mlab-modules/MPPB01/doc/parallella_schematic.pdf

# Page List

Page | Content

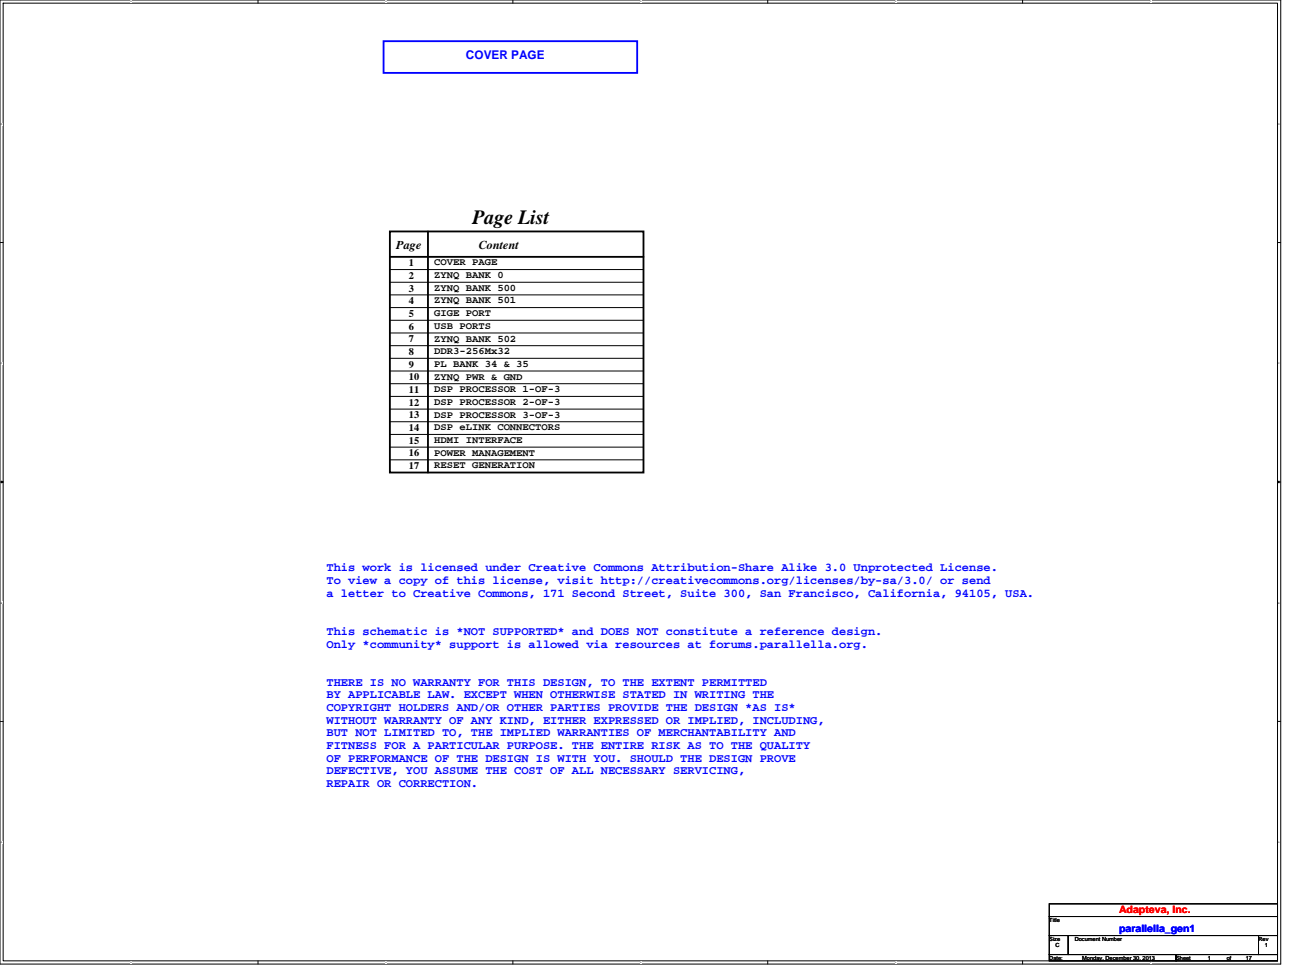
[picture p14: page 1]
COVER PAGE; Title; parallella_gen1; Adapteva, Inc.

1 | COVER PAGE
2 | ZYNQ BANK 0
3 | ZYNQ BANK 500
4 | ZYNQ BANK 501
5 | GIGE PORT
6 | USB PORTS
7 | ZYNQ BANK 502
8 | DDR3-256Mx32
9 | PL BANK 34 & 35
10 | ZYNQ PWR & GND
11 | DSP PROCESSOR 1-OF-3
12 | DSP PROCESSOR 2-OF-3
13 | DSP PROCESSOR 3-OF-3
14 DSP eLINK CONNECTORS
15 | HDMI INTERFACE
16 POWER MANAGEMENT
17 RESET GENERATION

This work is licensed under Creative Commons Attribution-Share Alike 3.0 Unprotected License.
To view a copy of this license, visit http://creativecommons.org/licenses/by-sa/3.0/ or send
a letter to Creative Commons, 171 Second Street, Suite 300, San Francisco, California, 94105, USA.

This schematic is *NOT SUPPORTED* and DOES NOT constitute a reference design.
Only *community* support is allowed via resources at forums.parallella.org.

THERE IS NO WARRANTY FOR THIS DESIGN, TO THE EXTENT PERMITTED
BY APPLICABLE LAW. EXCEPT WHEN OTHERWISE STATED IN WRITING THE
COPYRIGHT HOLDERS AND/OR OTHER PARTIES PROVIDE THE DESIGN *AS IS*
WITHOUT WARRANTY OF ANY KIND, EITHER EXPRESSED OR IMPLIED, INCLUDING,
BUT NOT LIMITED TO, THE IMPLIED WARRANTIES OF MERCHANTABILITY AND
FITNESS FOR A PARTICULAR PURPOSE. THE ENTIRE RISK AS TO THE QUALITY
OF PERFORMANCE OF THE DESIGN IS WITH YOU. SHOULD THE DESIGN PROVE
DEFECTIVE, YOU ASSUME THE COST OF ALL NECESSARY SERVICING,
REPAIR OR CORRECTION.

Size C | Document Number | Rev

Date: Monday, December 30, 2013 Monday, December 30, 2013 Monday, December 30, 2013 | Sheet 1 1 1 of 17 17 17

# ZYNQ BANK0

# BANK 0

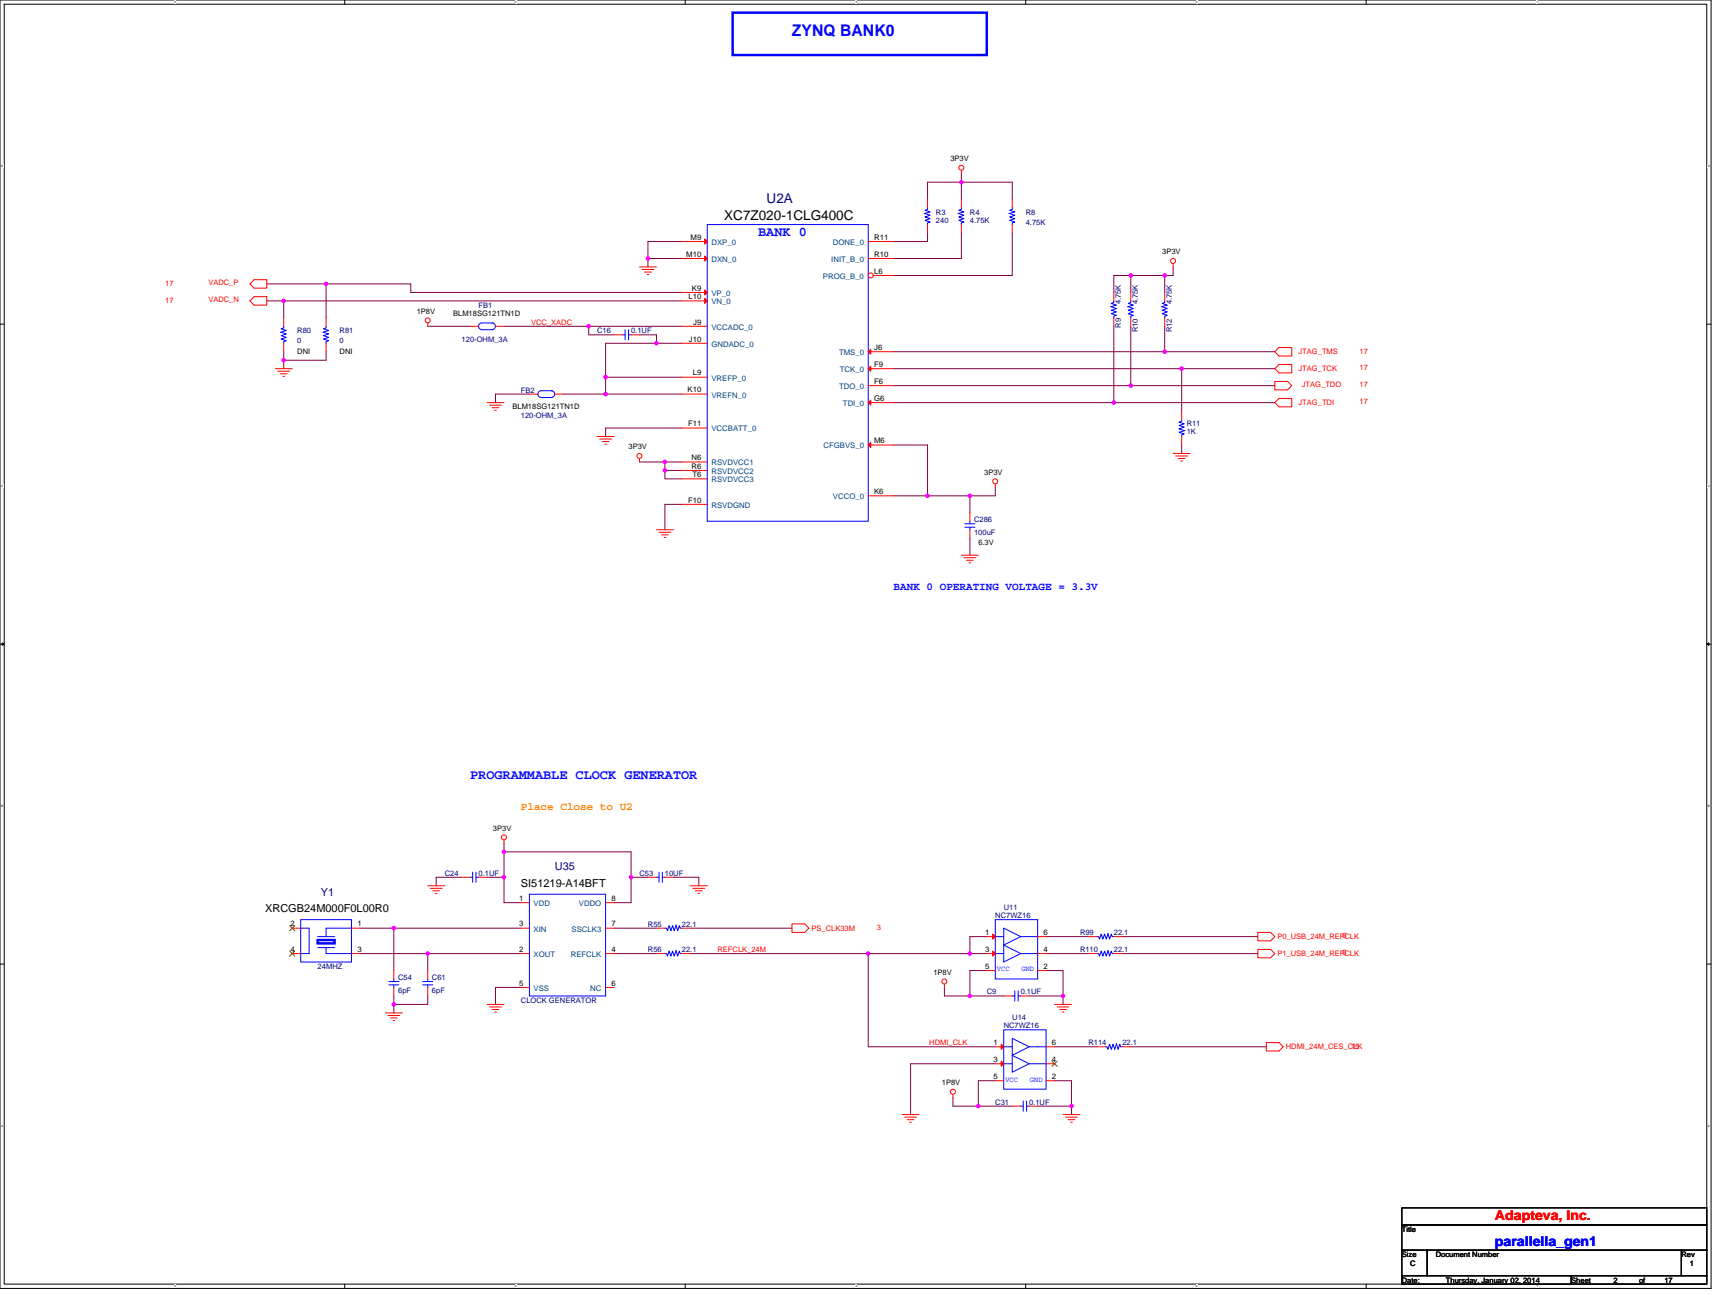
[picture p15: page 2]

# ZYNQ BANK 500

# QUAD SPI FLASH

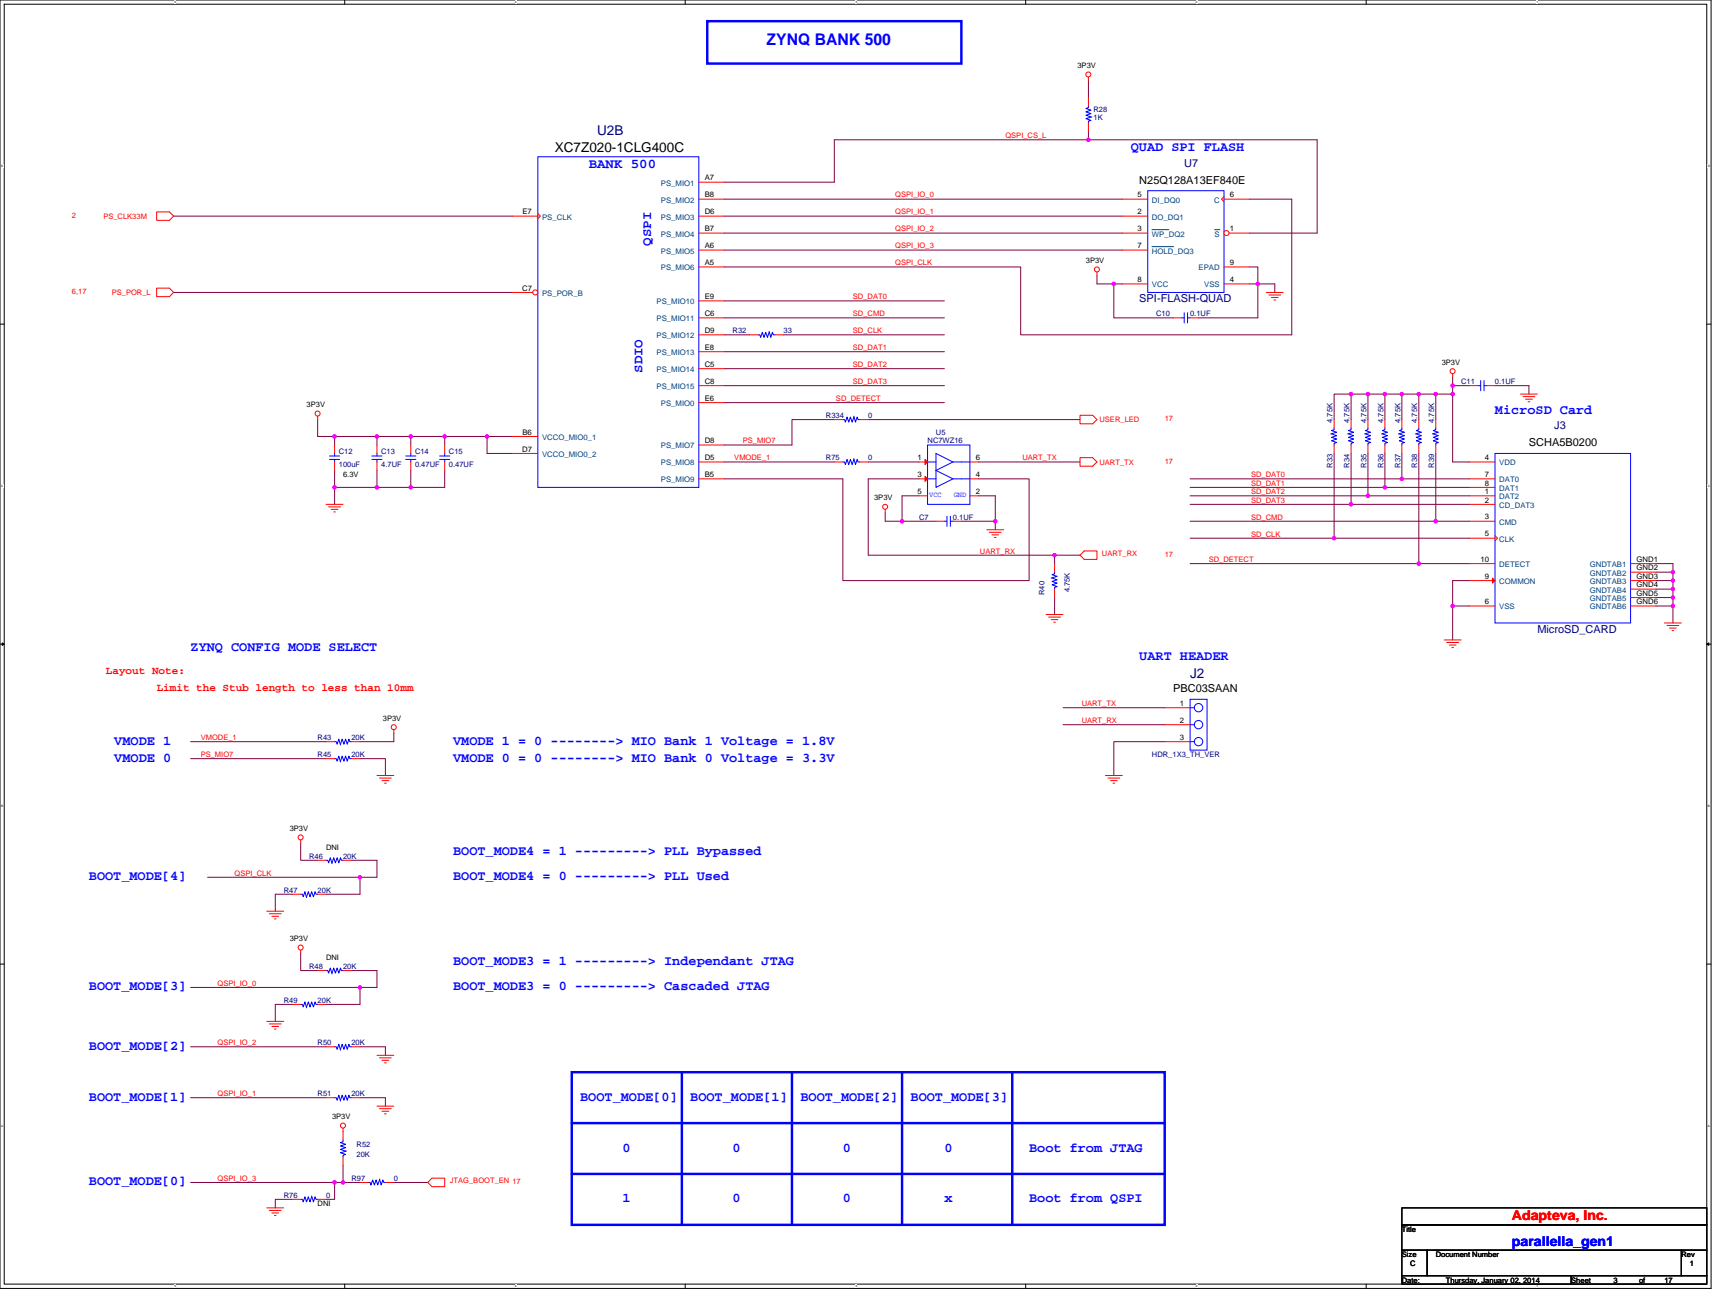
[picture p16: page 3]

ZYNQ CONFIG MODE SELECT

Limit the Stub length to less than 10mm

VMODE 1 = 0 --------> MIO Bank 1 Voltage = 1.8V
VMODE 0 = 0 --------> MIO Bank 0 Voltage = 3.3V

0 | 0 | 0 | 0 | Boot from JTAG

1 | | 0 0 | x | Boot from QSPI

# ZYNQ BANK 501

# BANK 501

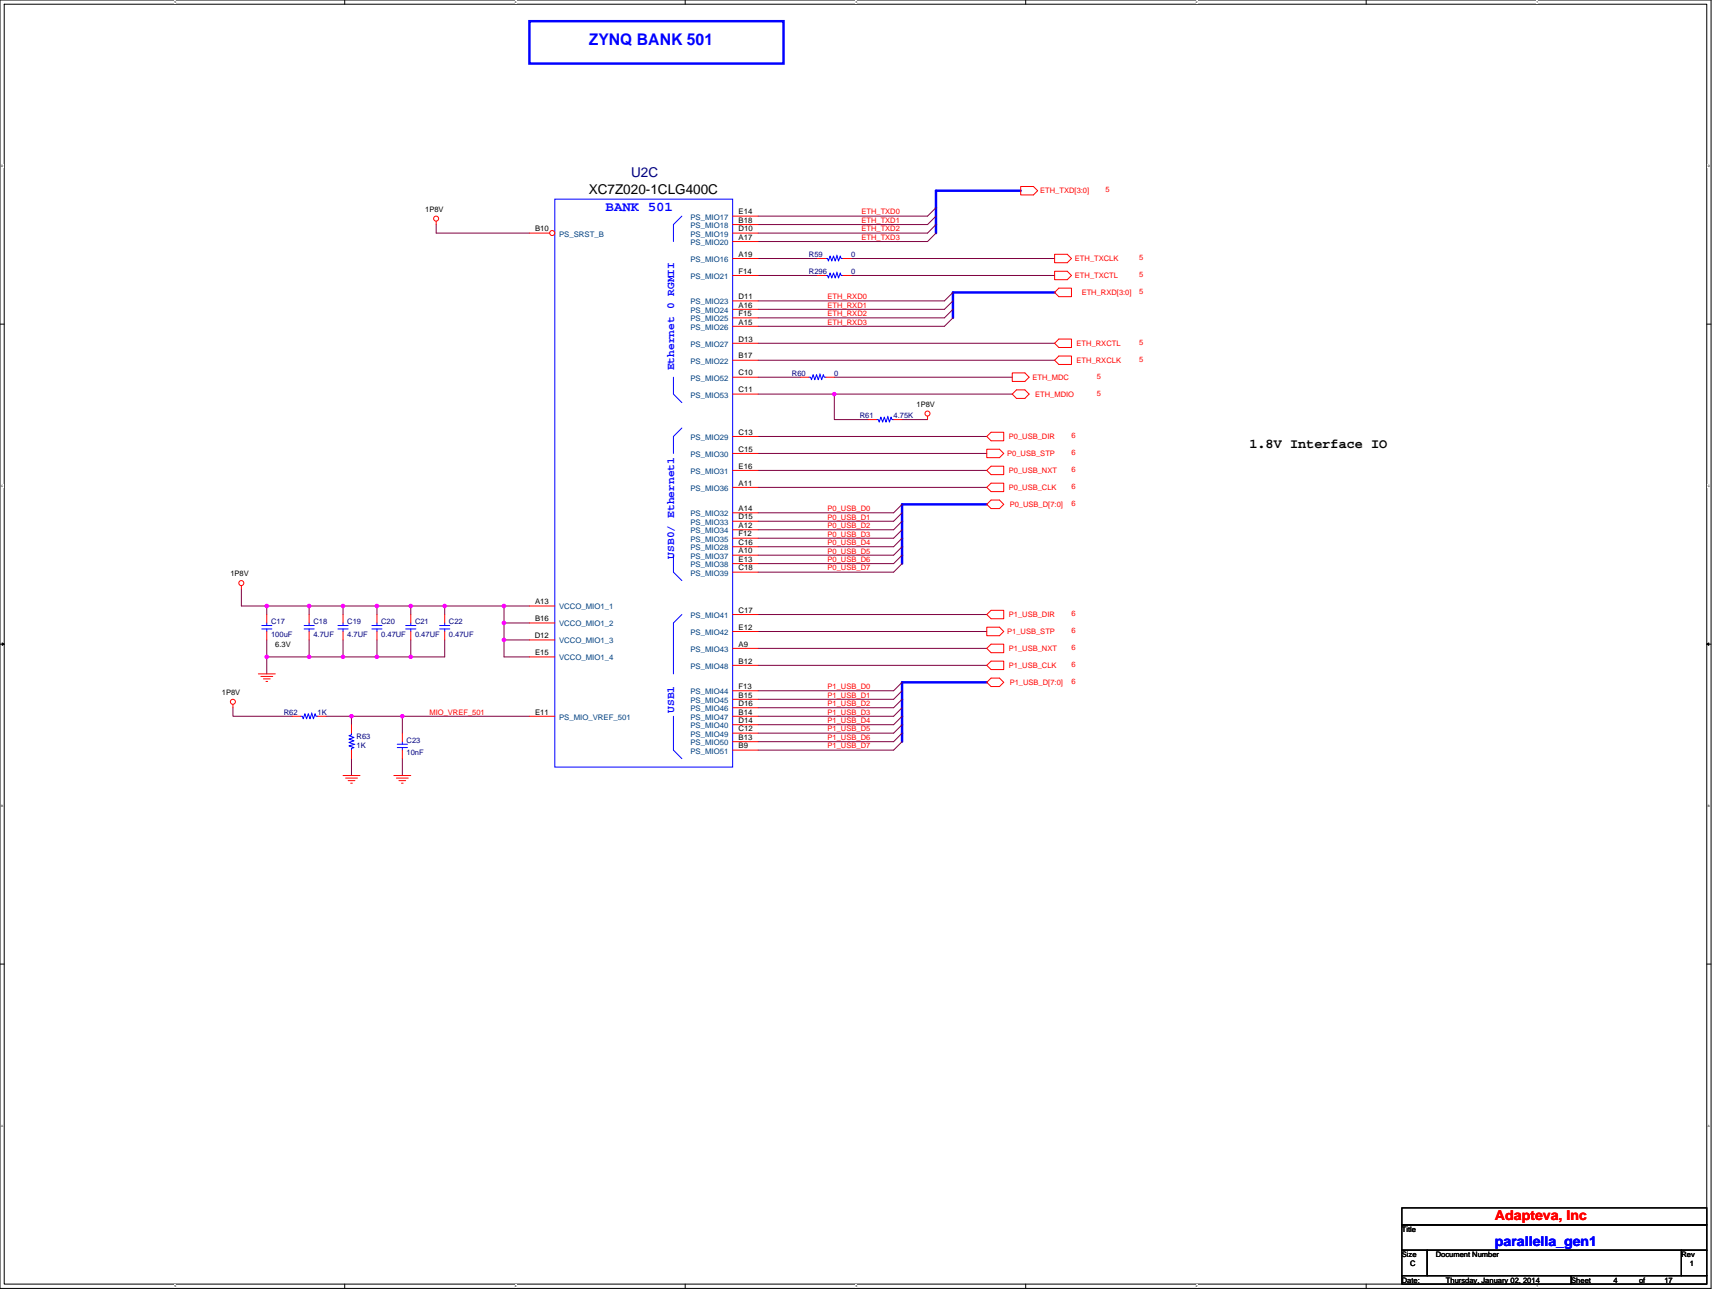
[picture p17: page 4]

## 100 Ohm Differential

# GIGE PHY

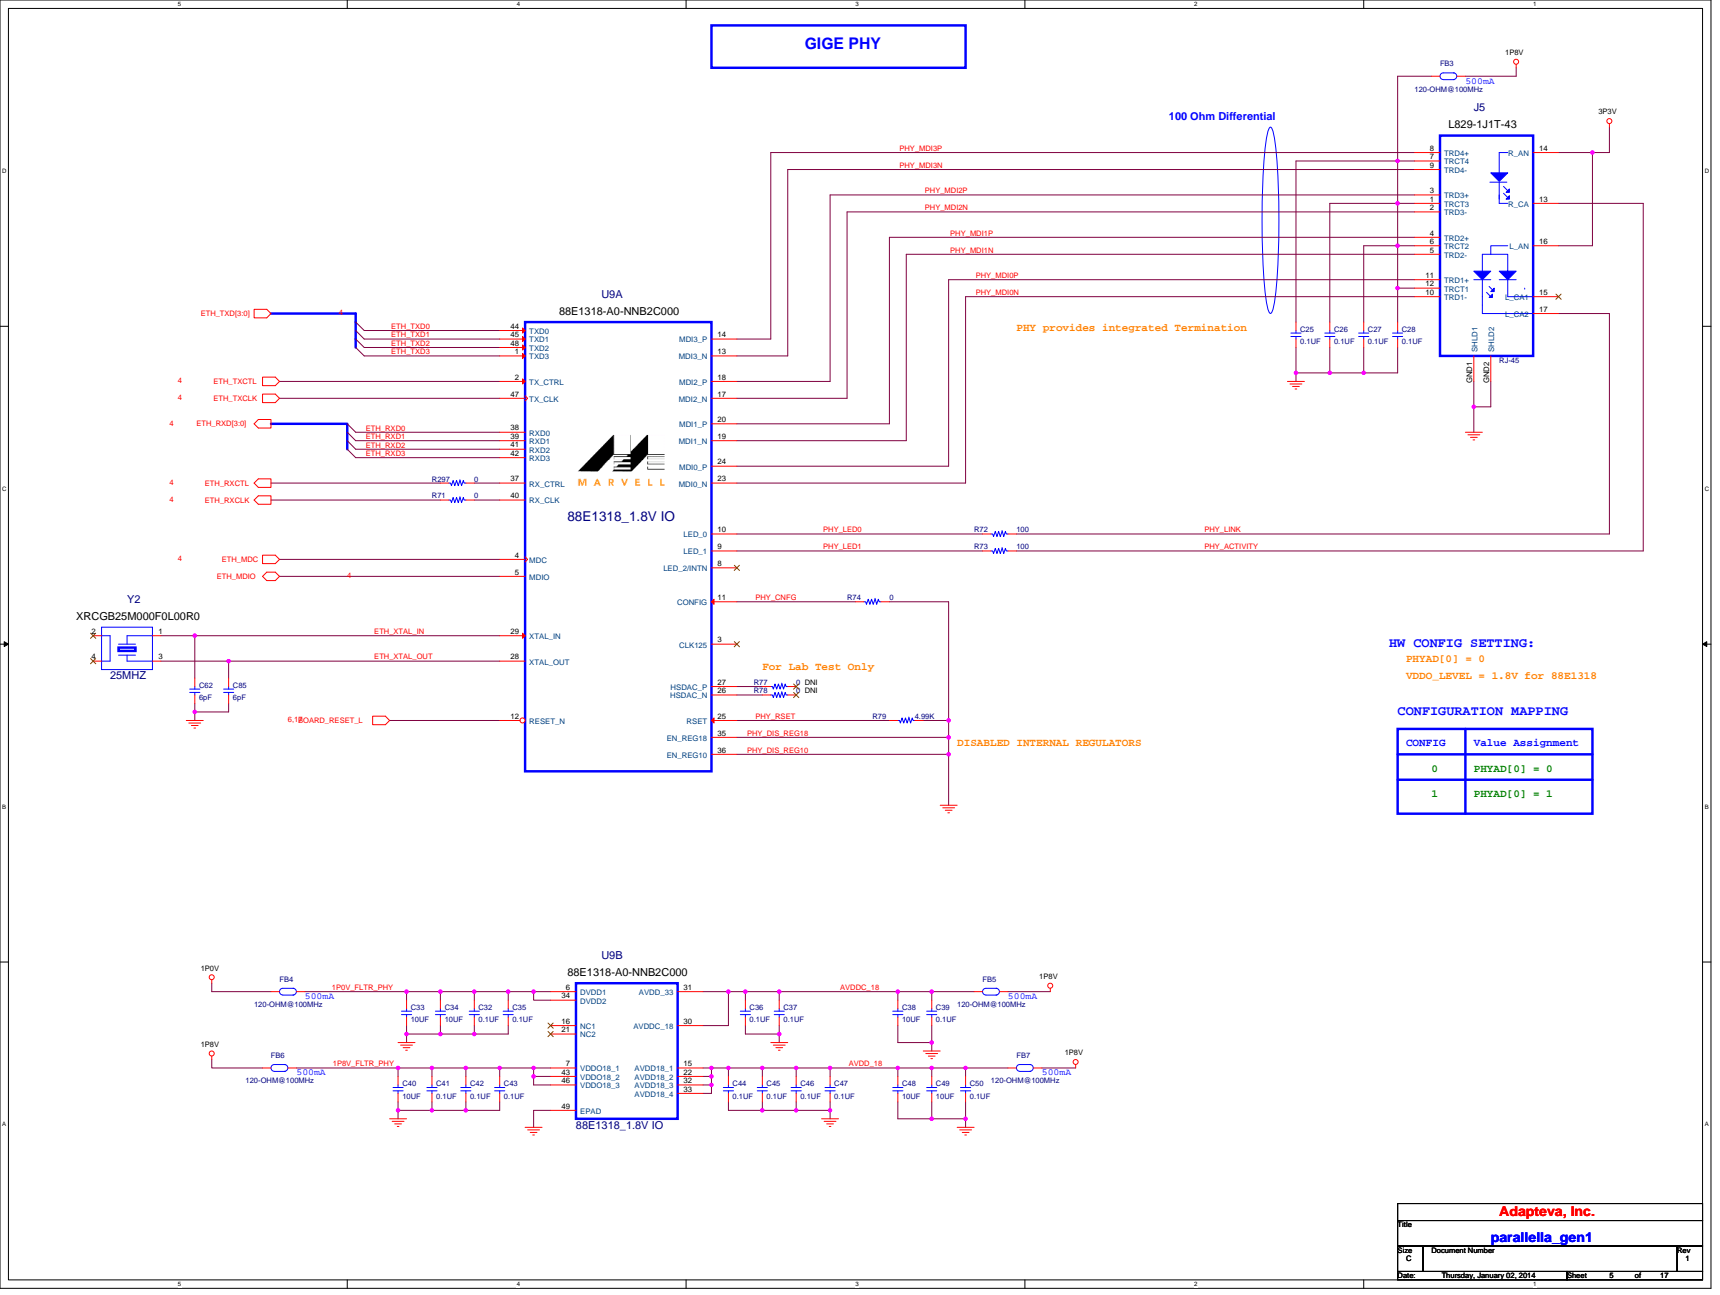
[picture p18: page 5]

TRCT4 7
TRD4- 9

PHY_MDI2P | | TRD3+ 3
PHY_MDI2N | | TRCT3 1

PHY_MDI1P | | TRD2+ 4
PHY_MDI1N | | | TRCT2 6

TRD2- 5

PHY_MDI0P | | TRCT1 12 TRD1+ 11

PHY_MDI0N

PHY provides integrated Termination

3 | ETH_XTAL_OUT | XTAL_OUT 28

For Lab Test Only

RESET_N 12

CONFIG | Value Assignment

0 | PHYAD[0] = 0

1 | PHYAD[0] = 1

# USB PORTS

## 100-ohm Differential

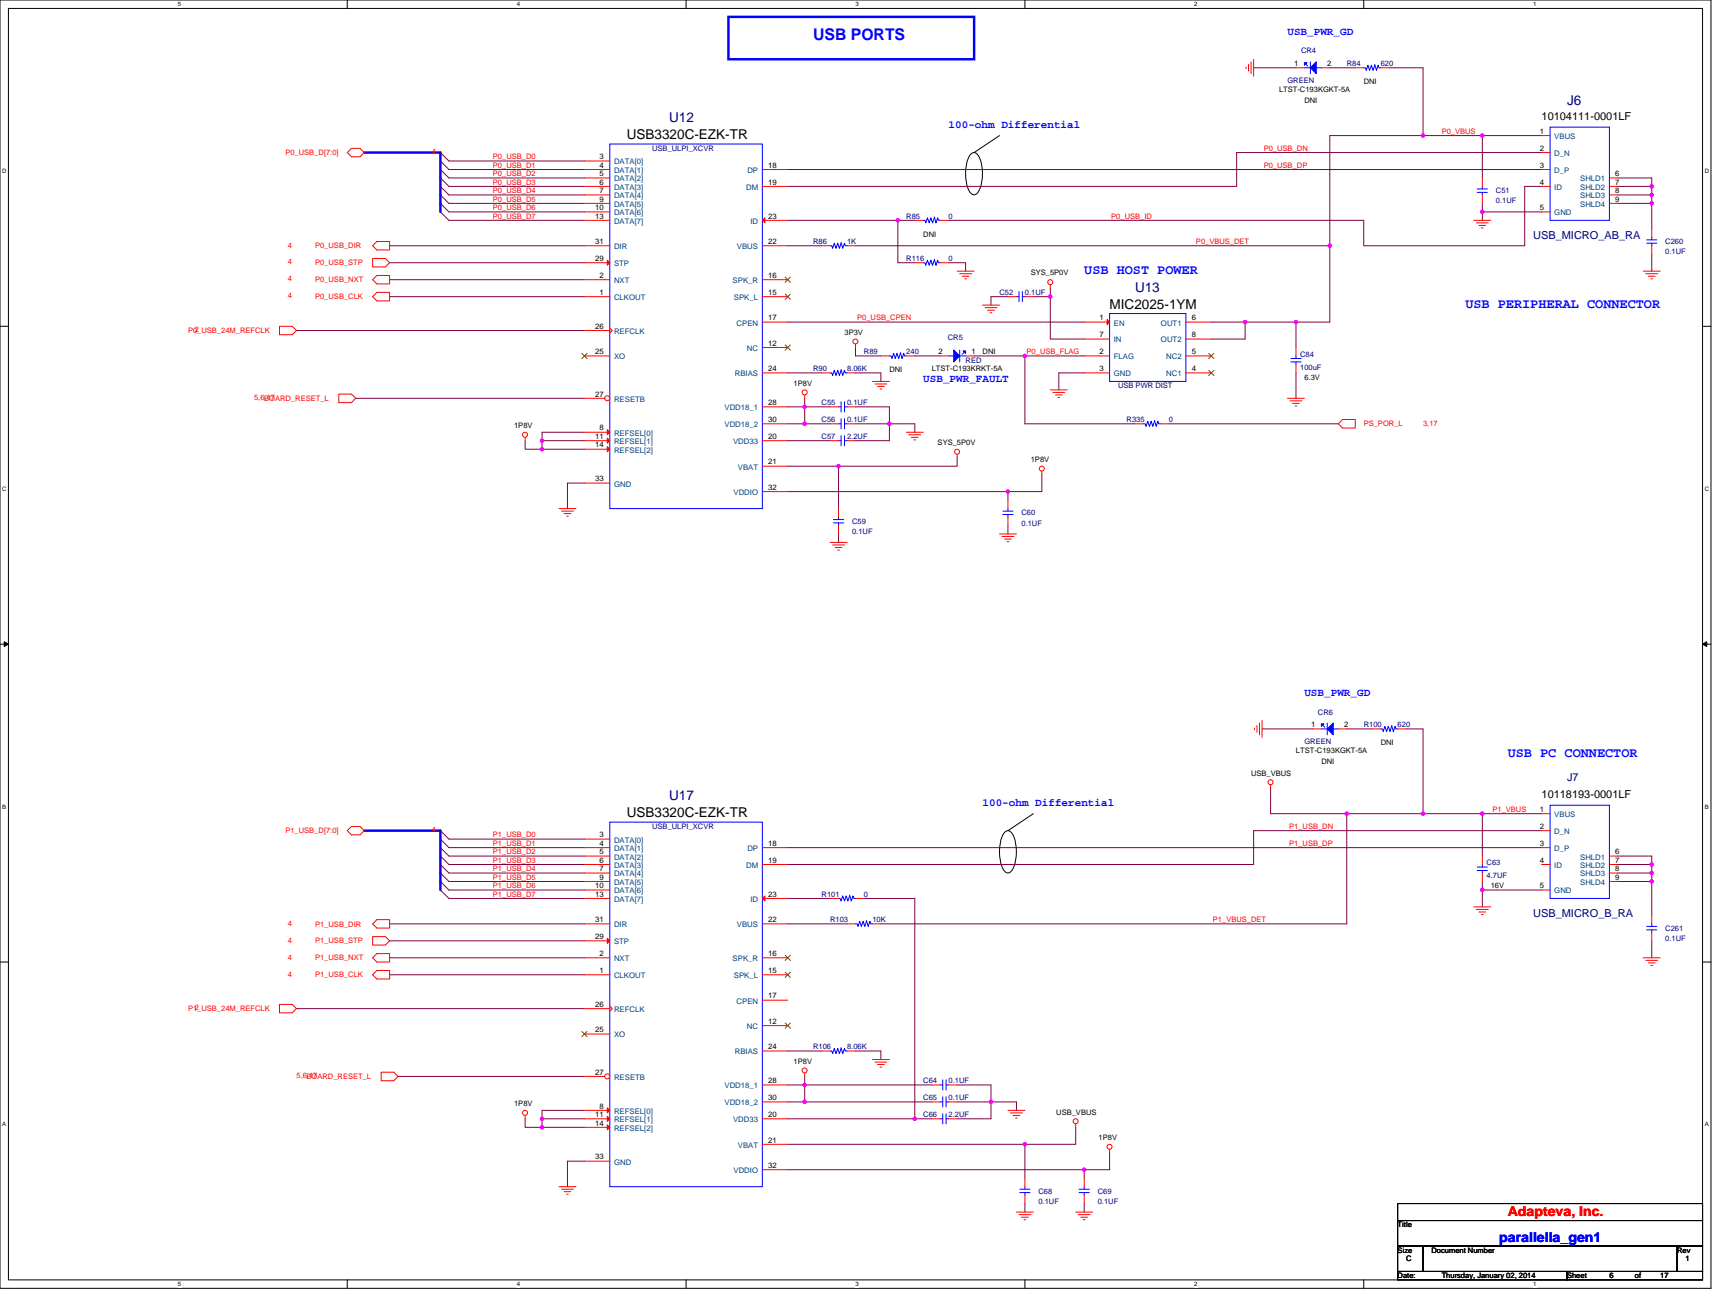
[picture p19: page 6]

P0_USB_DP | D_P 3

P1_USB_DP | | D_P 3

GND 5

# ZYNQ BANK 502

# BANK 502

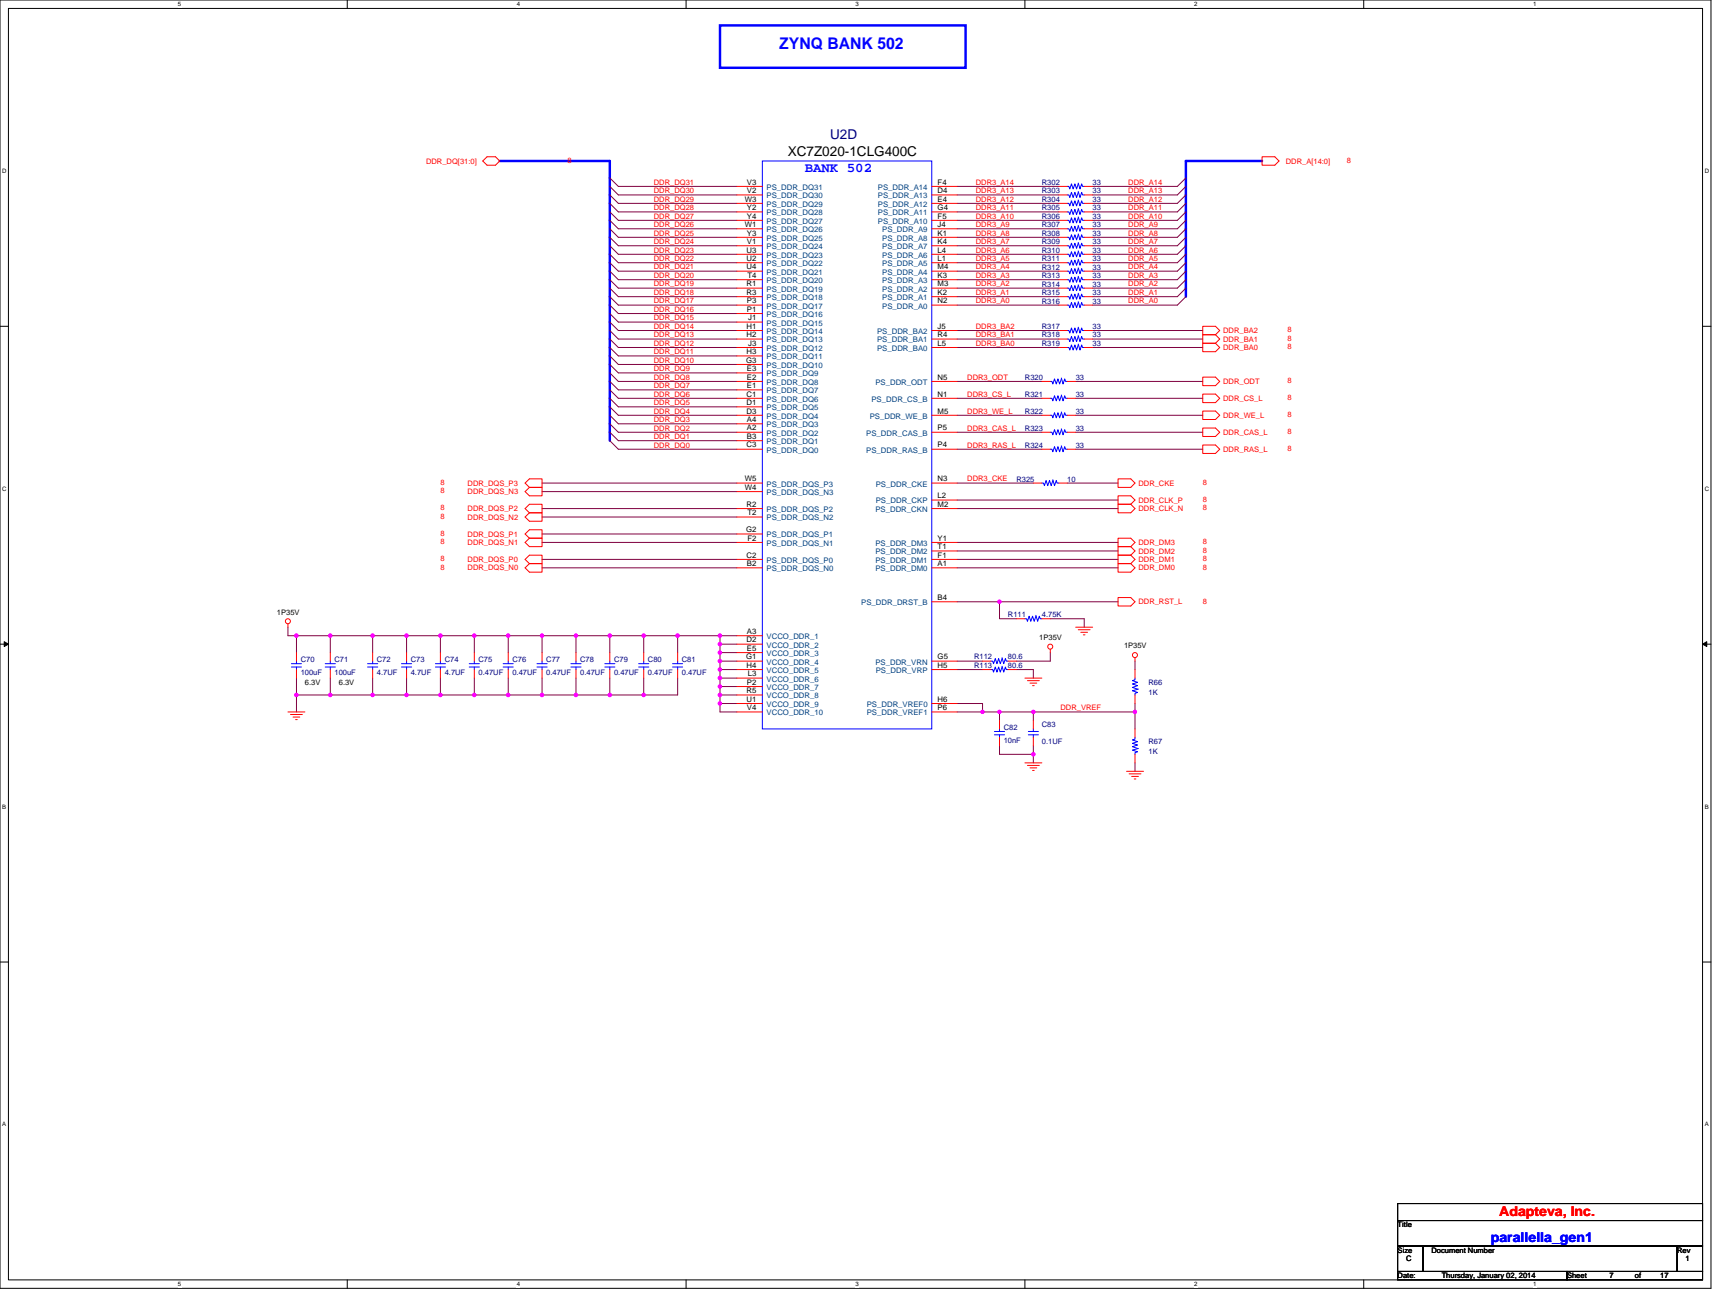
[picture p20: page 7]

# DDR3 - 256M X 32

U20

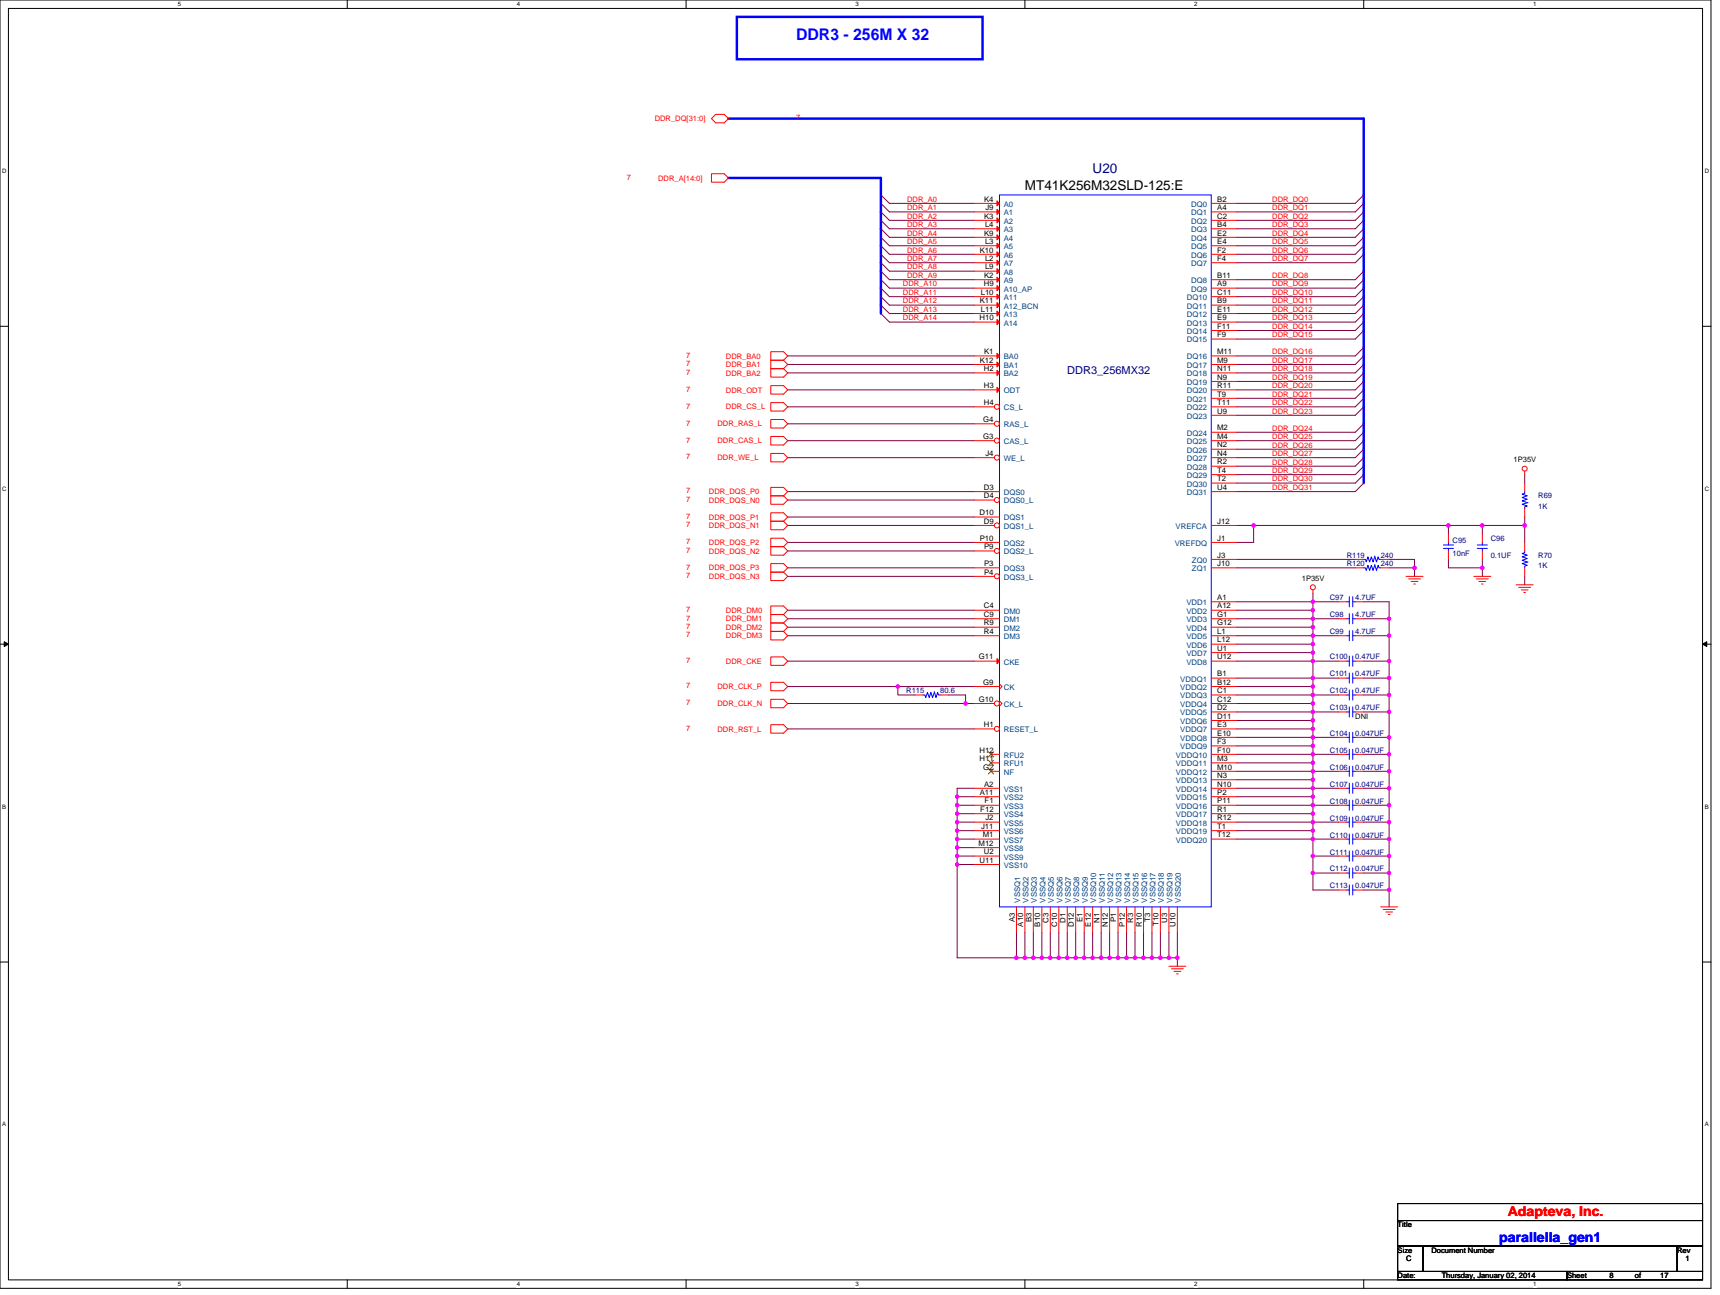
[picture p21: page 8]

# BANKS 34 & 35

# Enable 100-ohm internal termination on all LVDS inputs

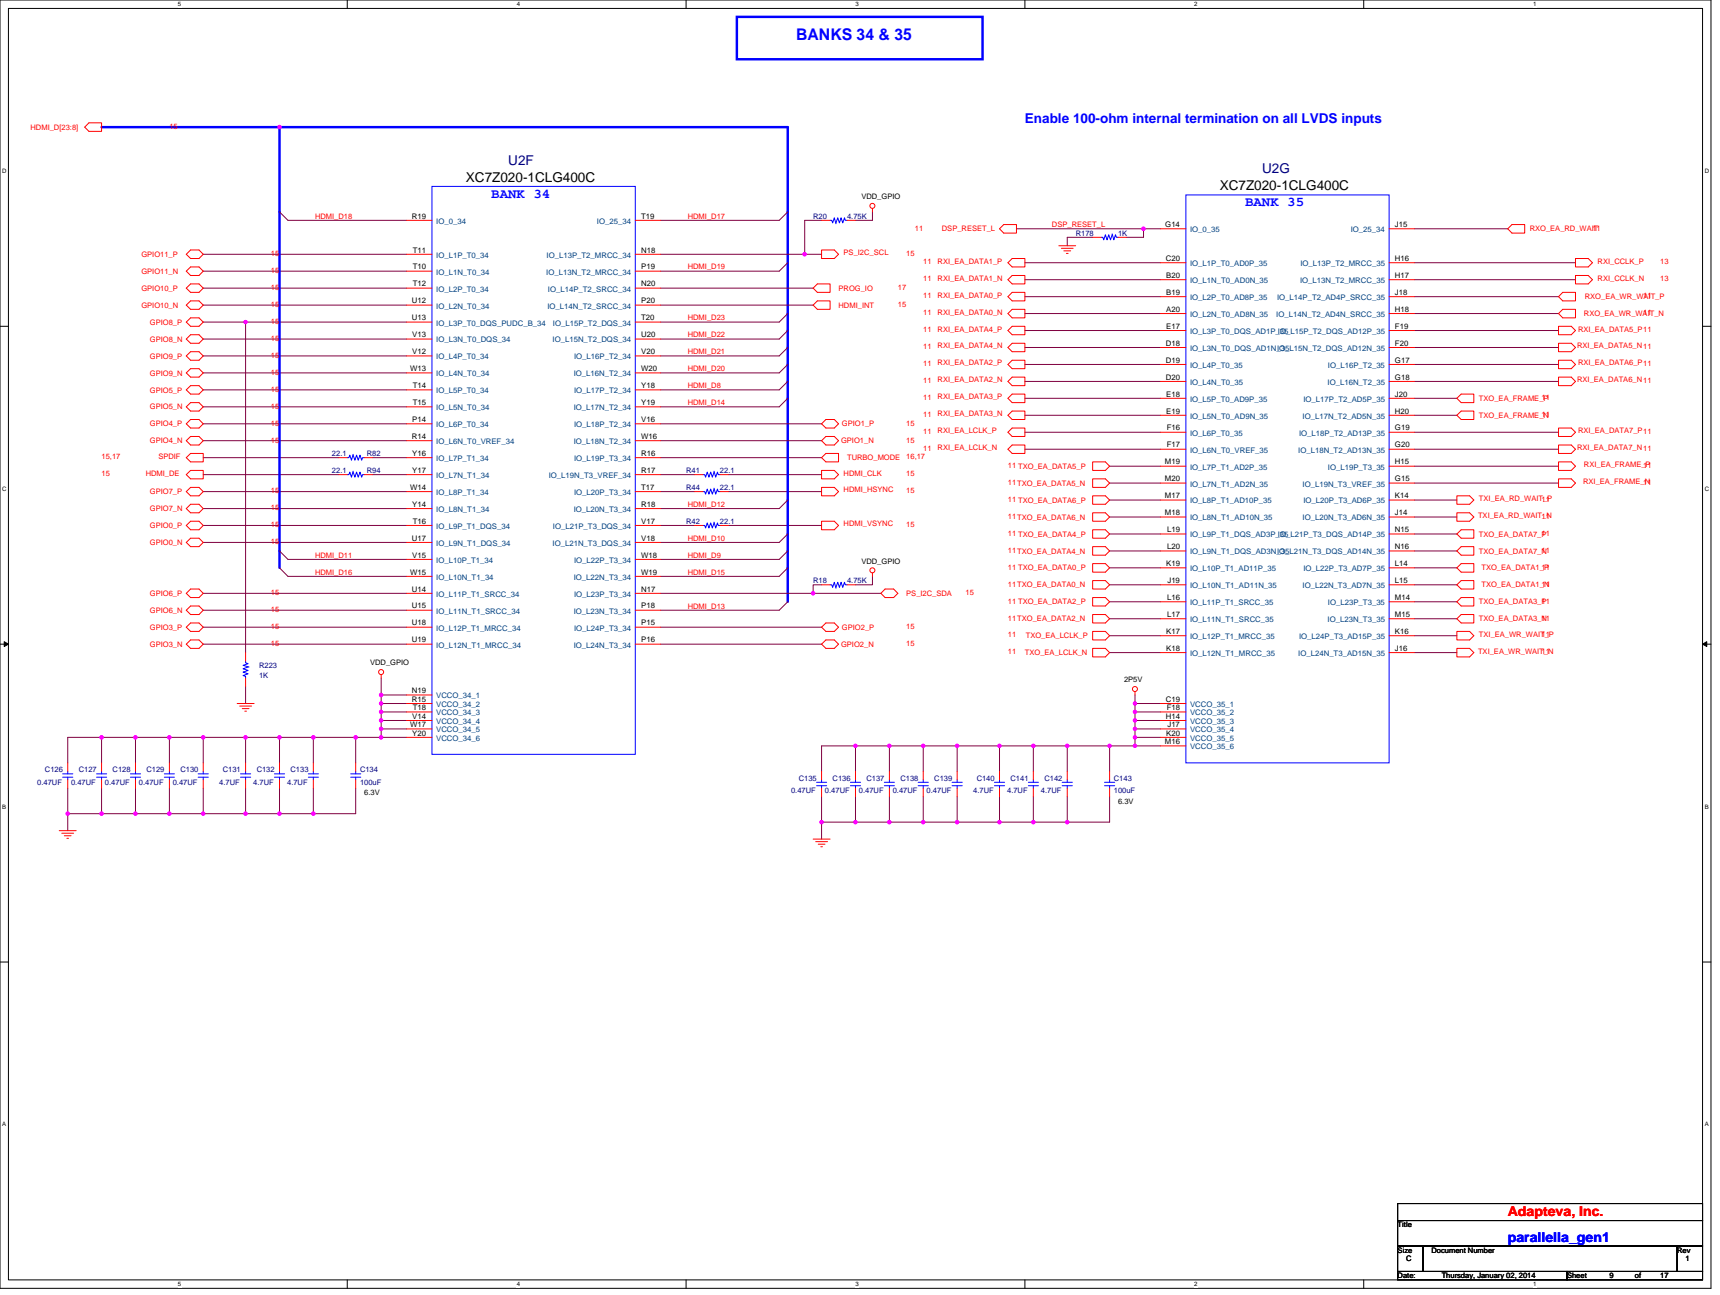
[picture p22: page 9]

IO_L3P_T0_DQS_PUDC_B_34 U13 | HDMI_D23 HDMI_D22 HDMI_D21 HDMI_D20 HDMI_D8 HDMI_D14

IO_L3N_T0_DQS_34 V13

IO_L6N_T0_VREF_34 R14

IO_L9N_T1_DQS_34 U17

# ZYNQ POWER & GROUND

# PWR/GND

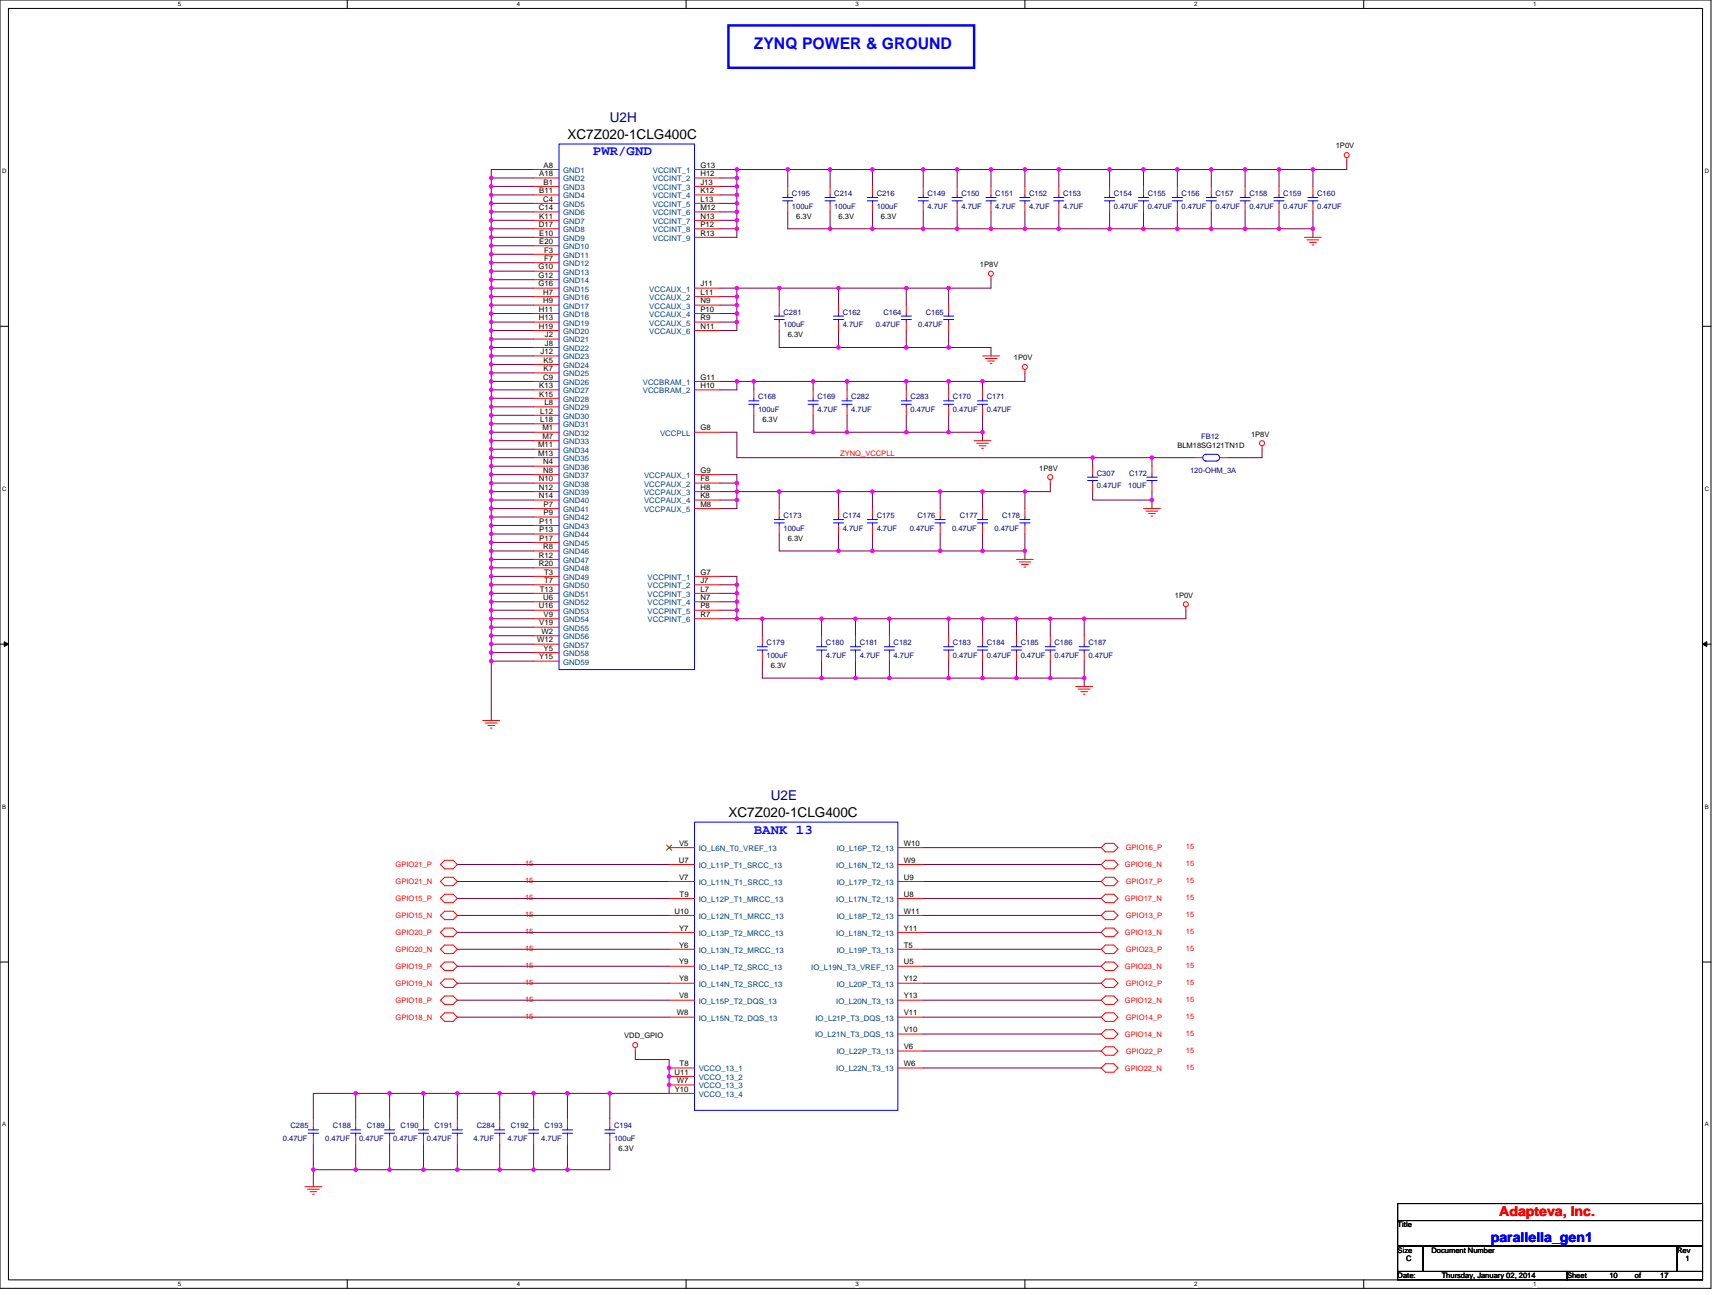
[picture p23: page 10]

# DSP PROCESSOR 1-OF-3

# CONTROL/MONITOR

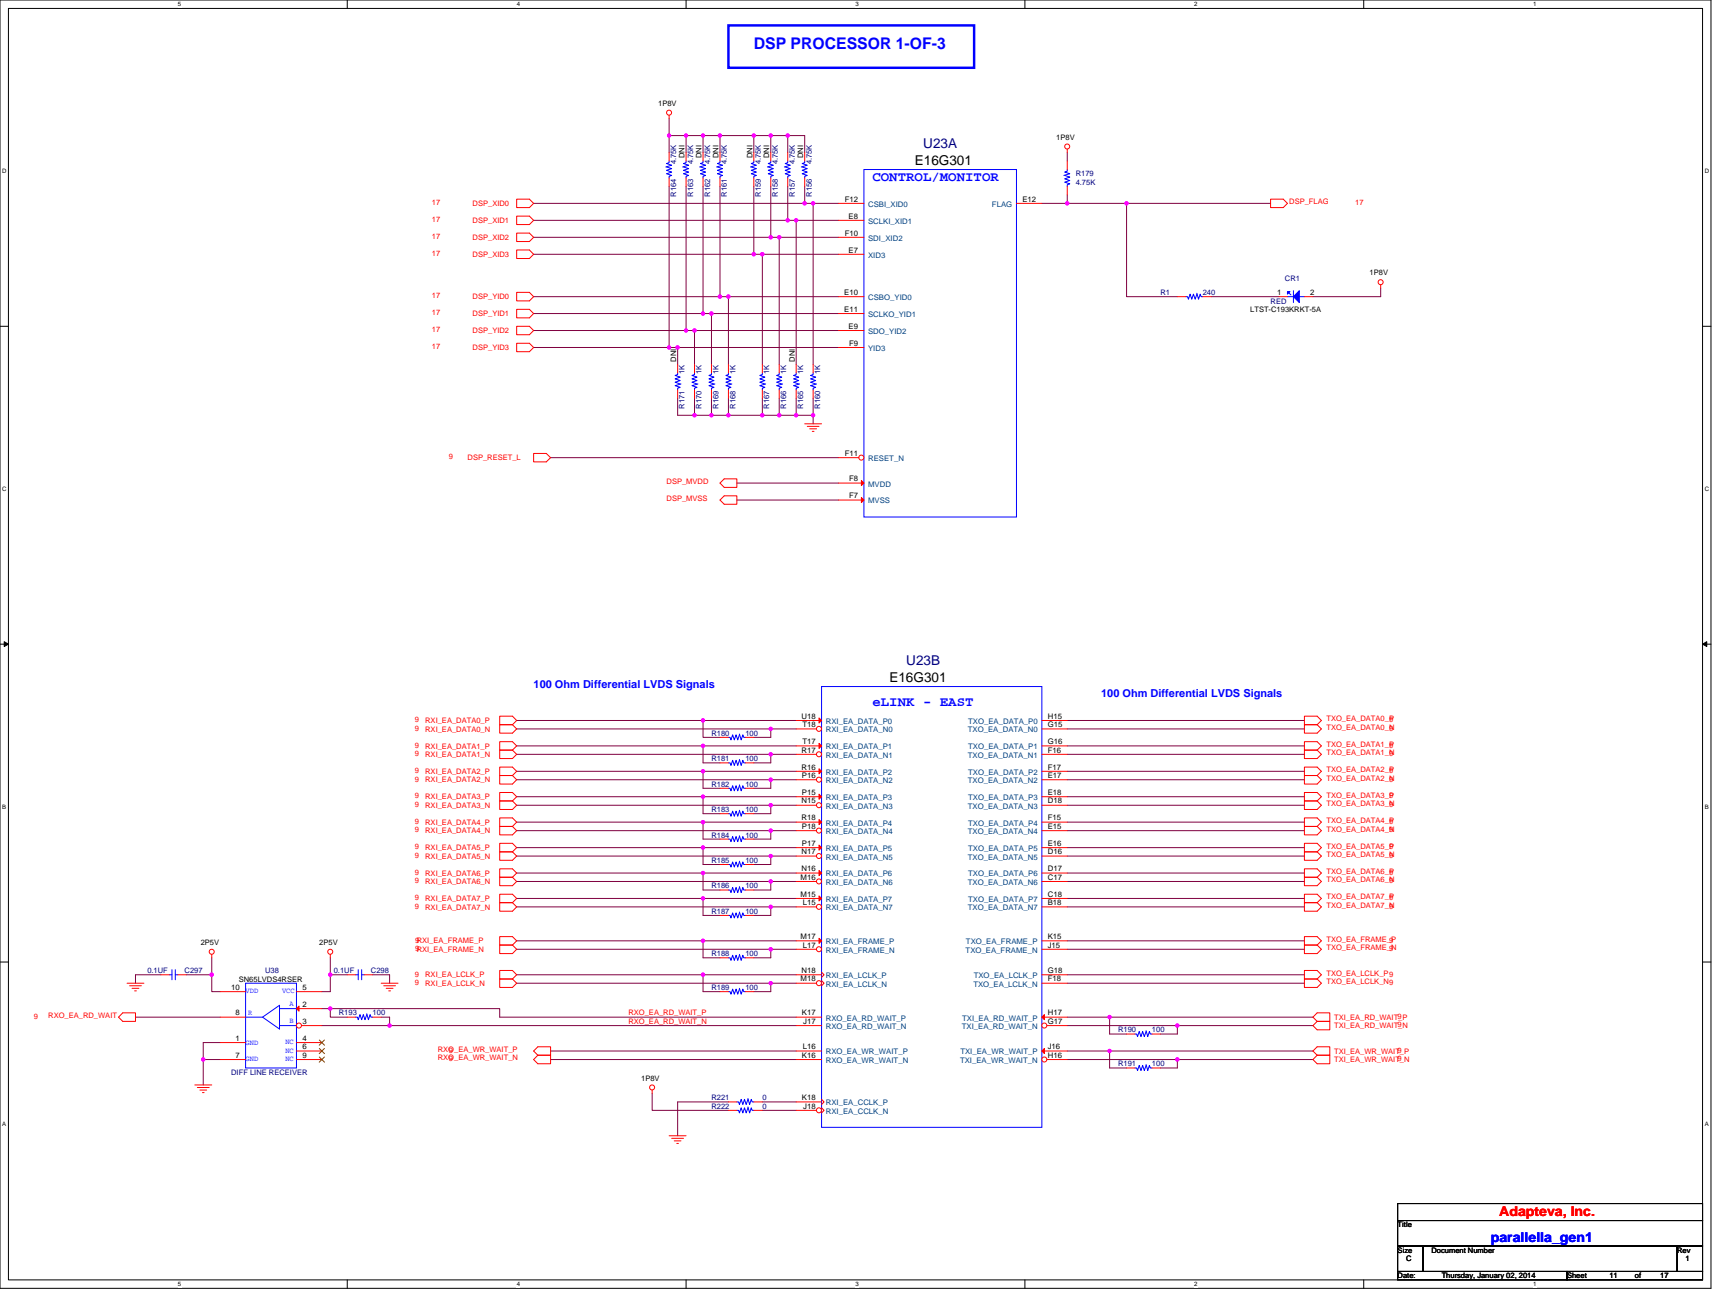
[picture p24: page 11]

SCLKI_XID1 E8

SDI_XID2 F10

XID3 E7

CSBO_YID0 E10

SCLKO_YID1 E11

SDO_YID2 E9

YID3 F9

100 Ohm Differential LVDS Signals

RXI_EA_DATA_N1 R17 RXI_EA_DATA_P2 R16

RXI_EA_DATA_N2 P16 RXI_EA_DATA_P3 P15

RXI_EA_DATA_N3 N15 RXI_EA_DATA_P4 R18

RXI_EA_DATA_N4 P18 RXI_EA_DATA_P5 P17

RXI_EA_DATA_N5 N17 RXI_EA_DATA_P6 N16

RXI_EA_DATA_N6 M16 RXI_EA_DATA_P7 M15

100 Ohm Differential LVDS Signals | 100 Ohm Differential LVDS Signals

# DSP PROCESSOR 2-OF-3

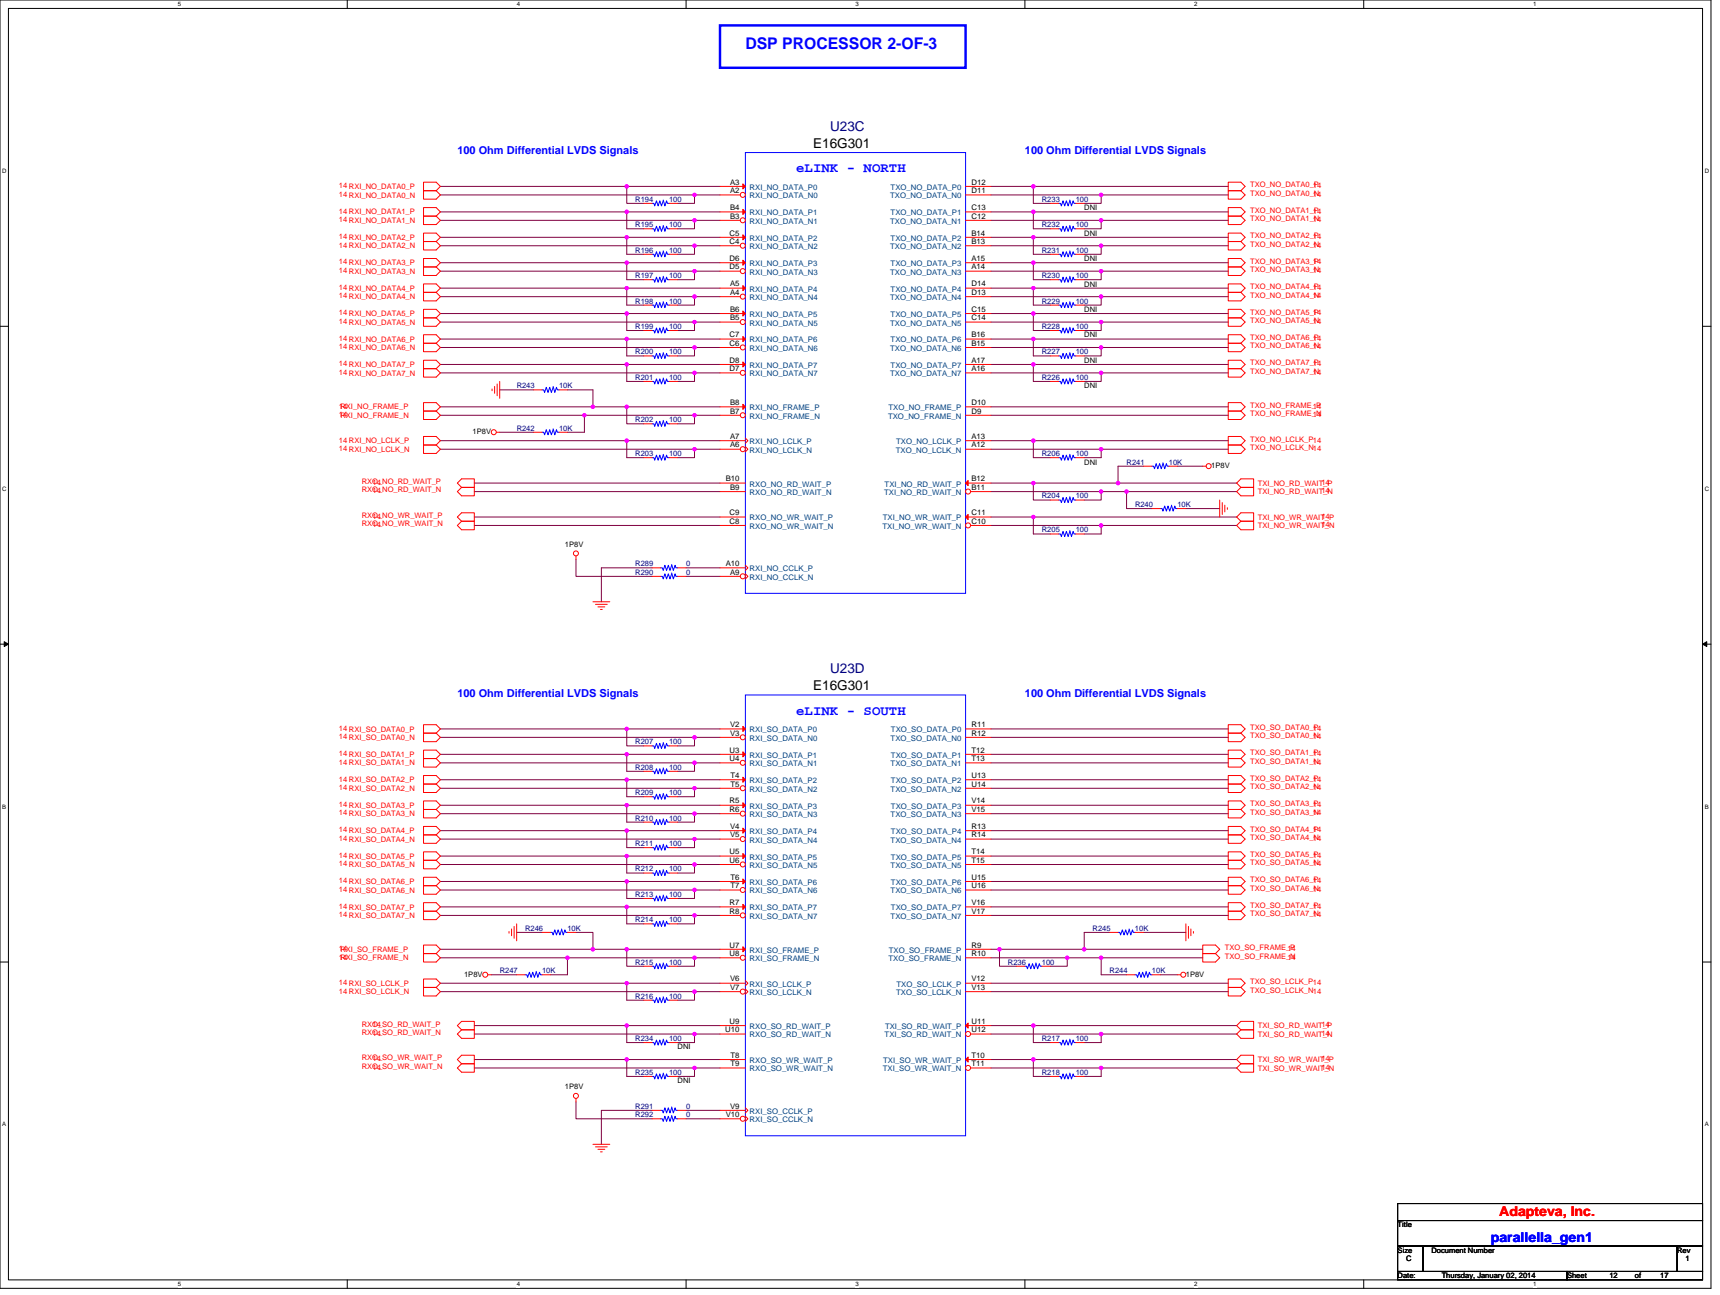
[picture p25: page 12]

# DSP PROCESSOR 3-OF-3

# POWER/GROUND

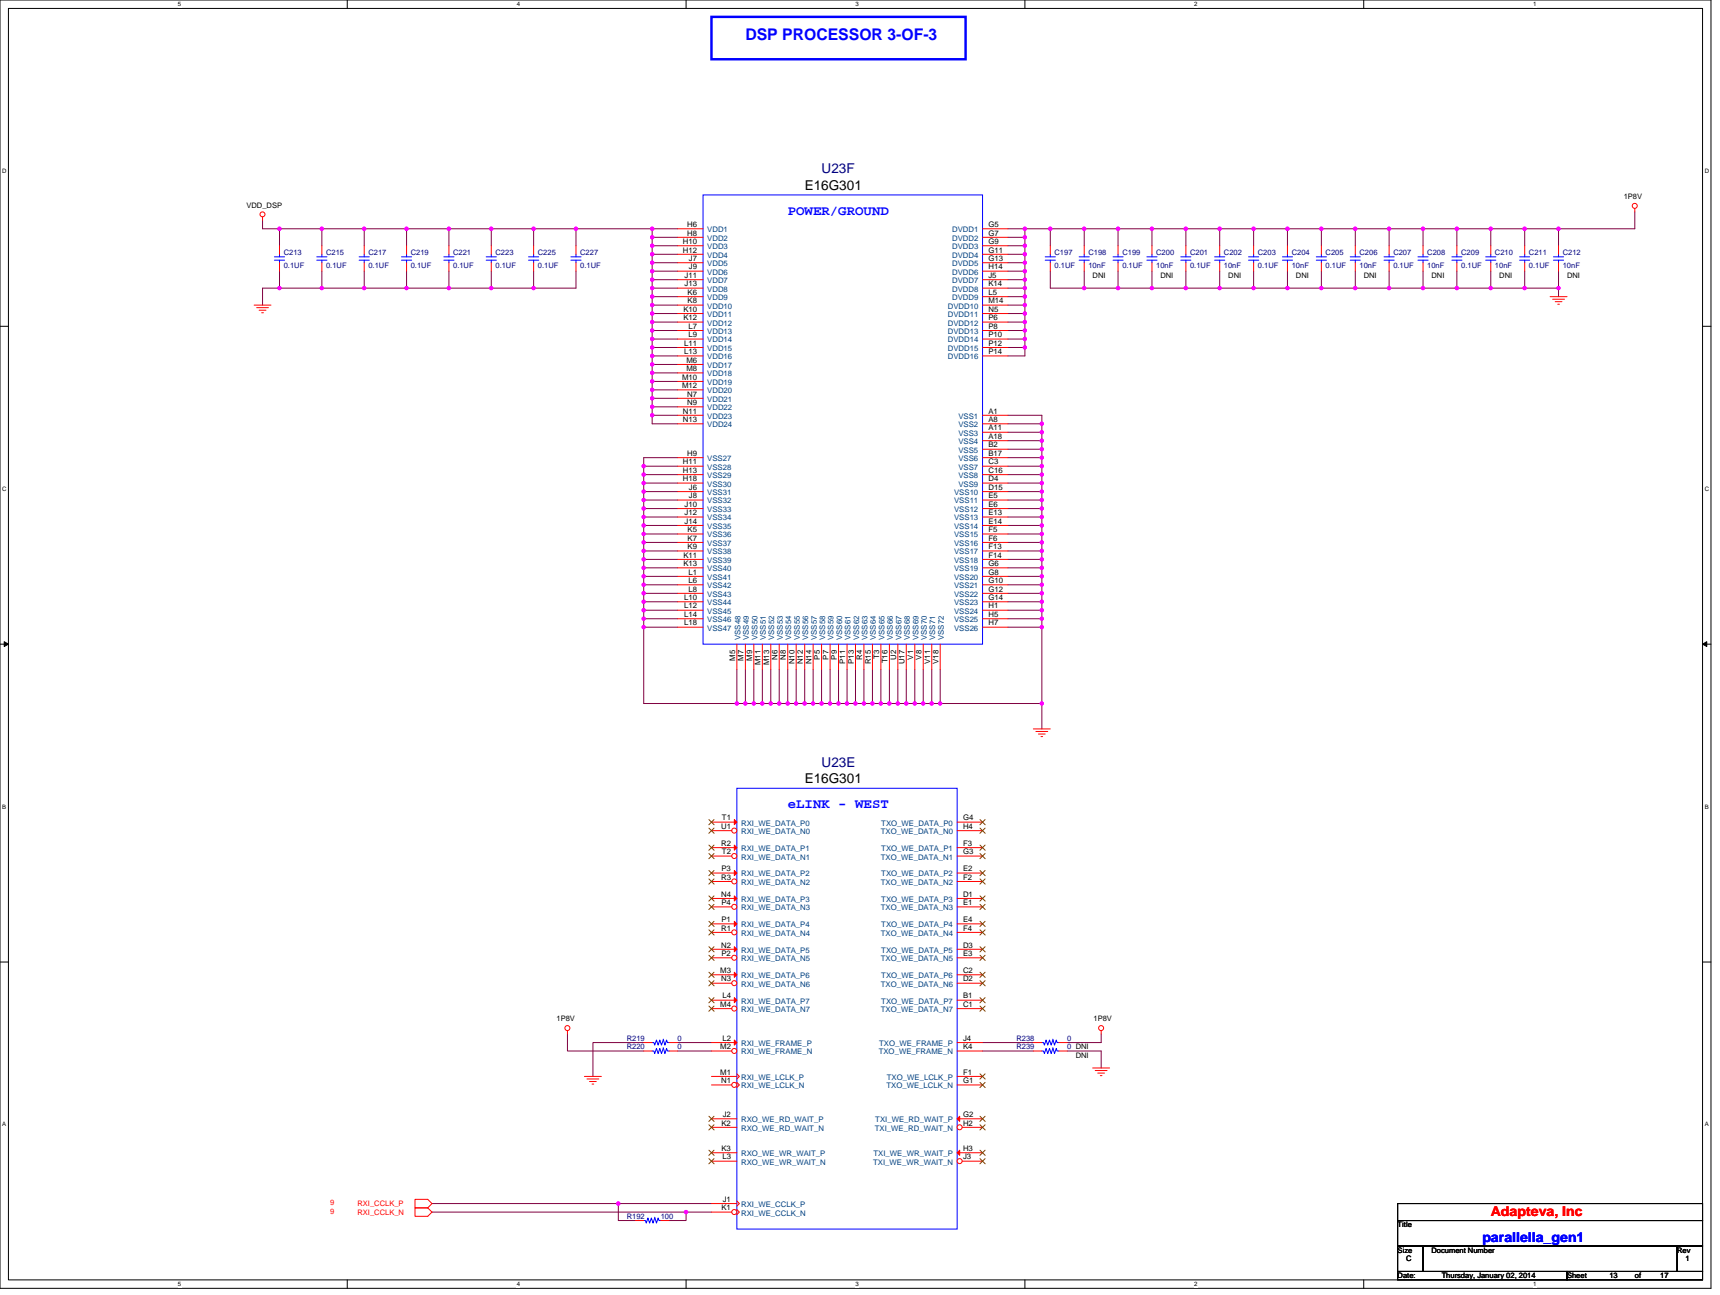
[picture p26: page 13]

# DSP eLINK CONNECTORS

# eLINK North Connector

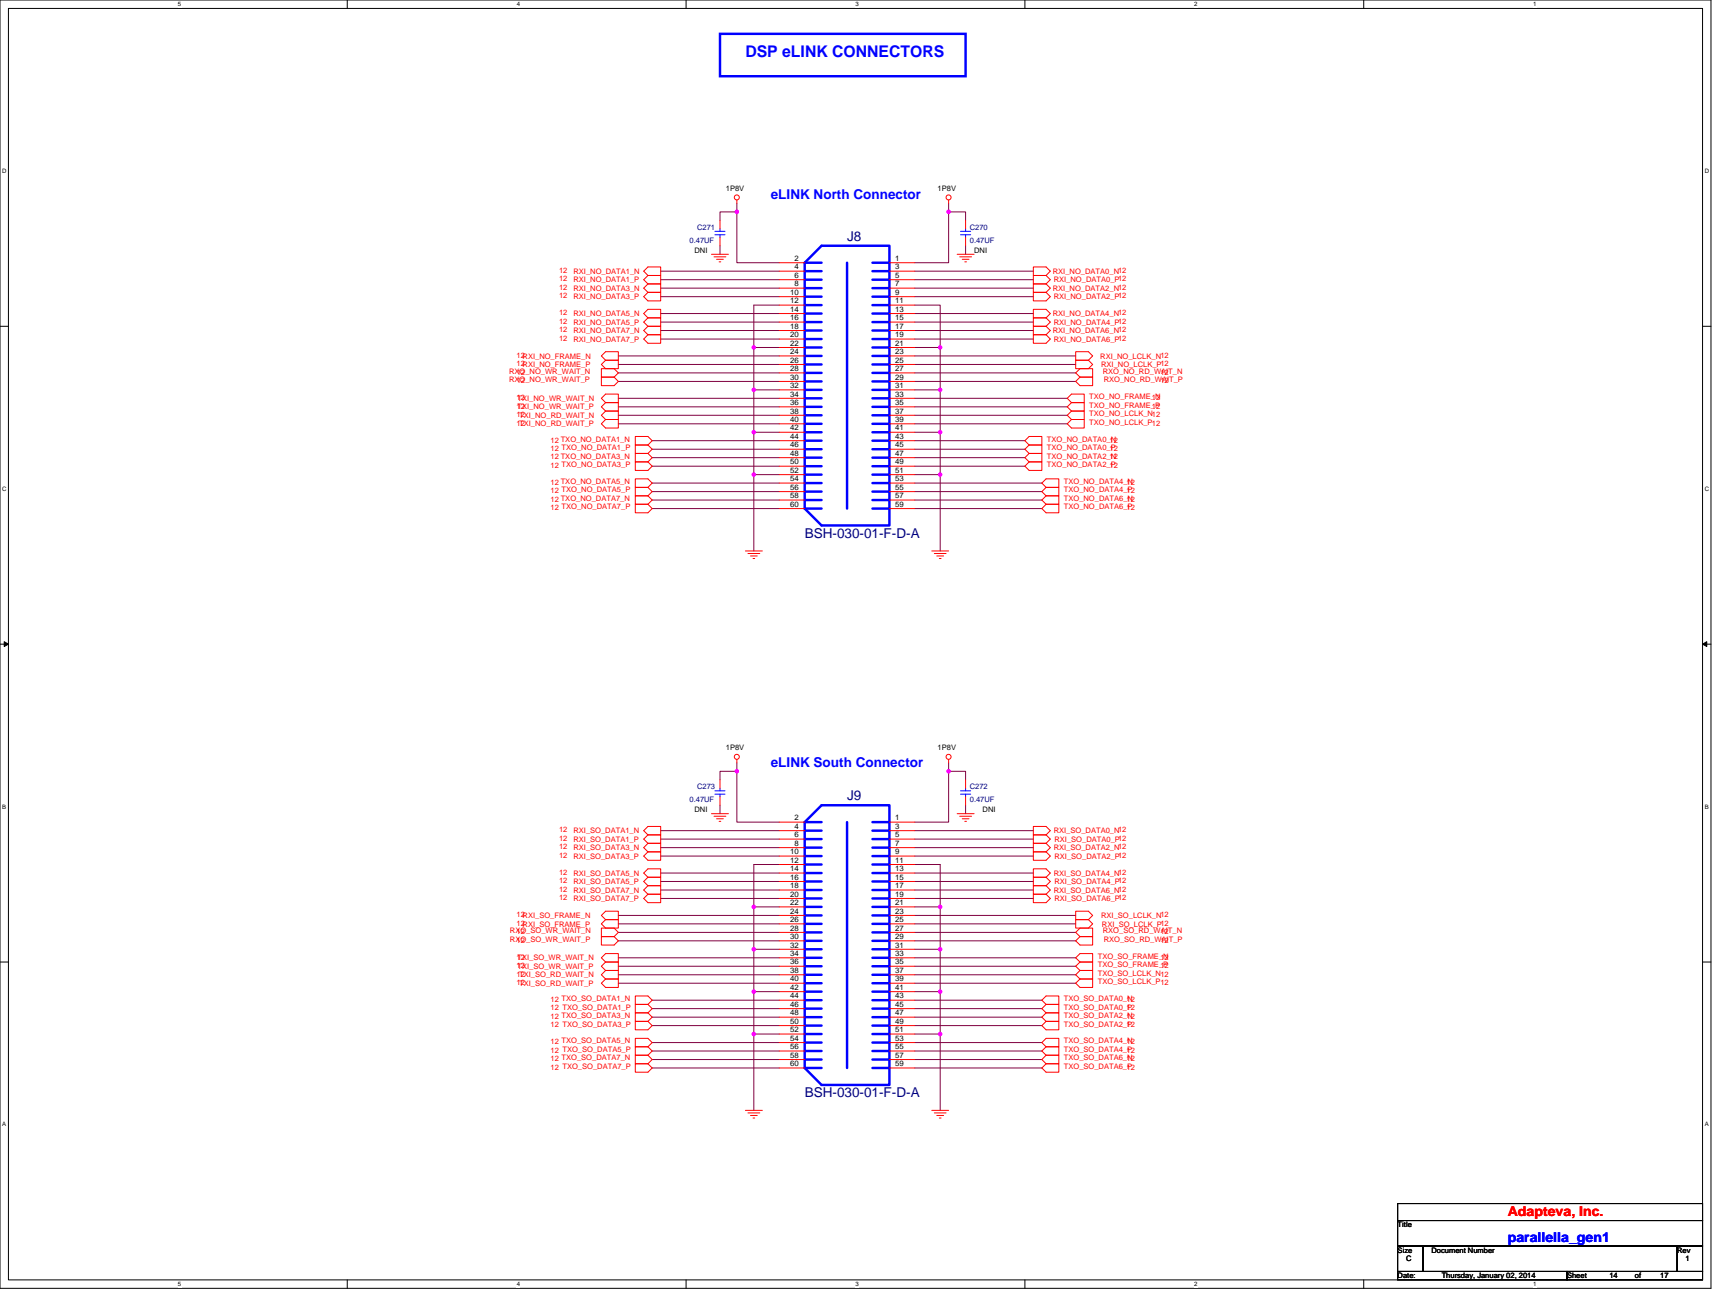
[picture p27: page 14]
RXI_NO_DATA0_P12; RXI_NO_DATA0_N12; RXI_NO_DATA4_P12; RXI_NO_DATA4_N12; 12 RXI_NO_DATA1_P; 12 RXI_NO_DATA1_N; RXI_NO_DATA6_P12; RXI_NO_DATA6_N12; 12 RXI_NO_DATA7_P; 12 RXI_NO_DATA7_N; RXI_NO_LCLK_P12; RXI_NO_LCLK_N12; 12RXI_NO_FRAME_P; 12RXI_NO_FRAME_N; 12 RXI_NO_DATA3_P; 12 RXI_NO_DATA3_N; TXO_NO_DATA4_P12; TXO_NO_DATA4_N12; 12 TXO_NO_DATA5_P; 12 TXO_NO_DATA5_N; TXO_NO_DATA6_P12; TXO_NO_DATA6_N12; 12 TXO_NO_DATA7_P; 12 TXO_NO_DATA7_N; TXO_NO_DATA0_P12; TXO_NO_DATA0_N12; 12 TXO_NO_DATA1_P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

eLINK South Connector

# HDMI TRANSMITTER

U37

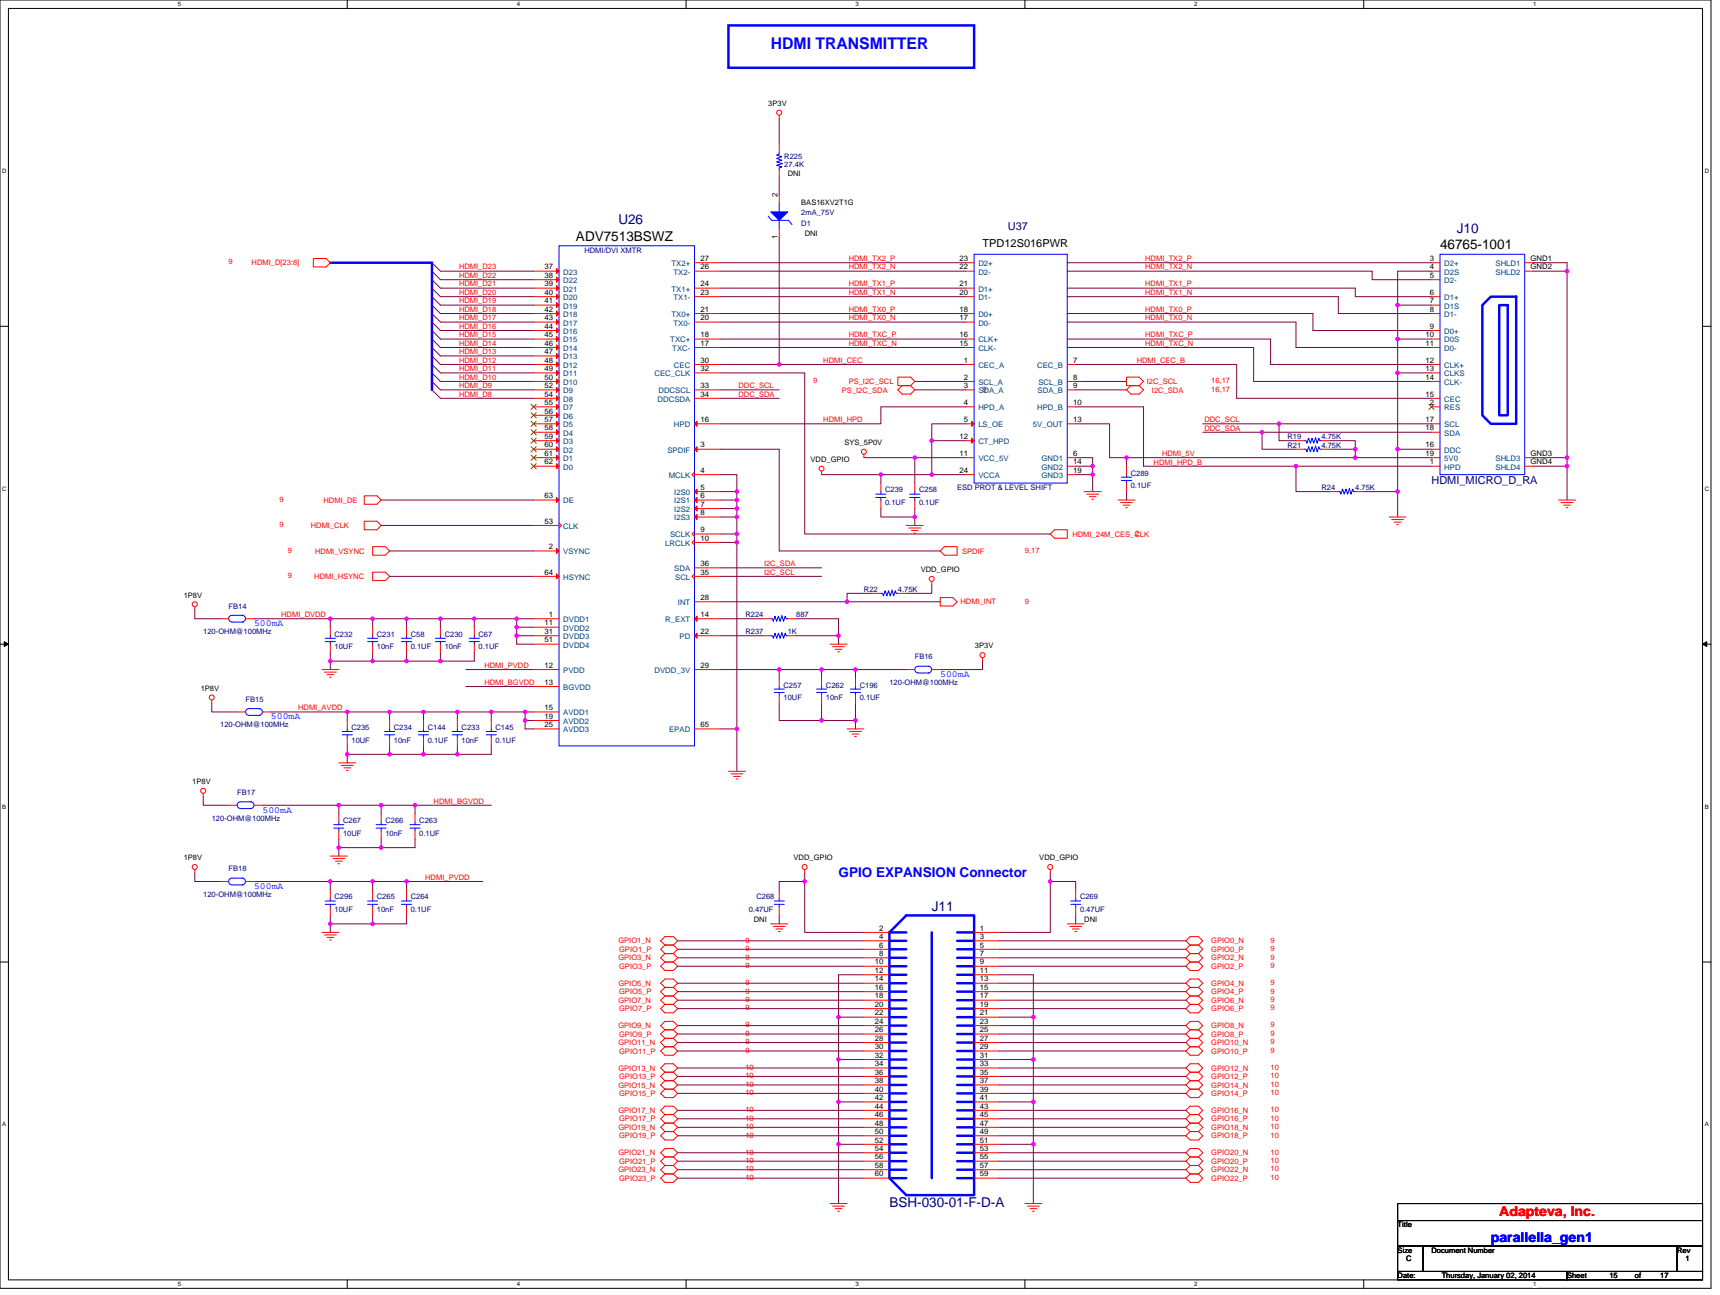
[picture p28: page 15]

ESD PROT & LEVEL SHIFT

# POWER MANAGEMENT

## 5A TRACE

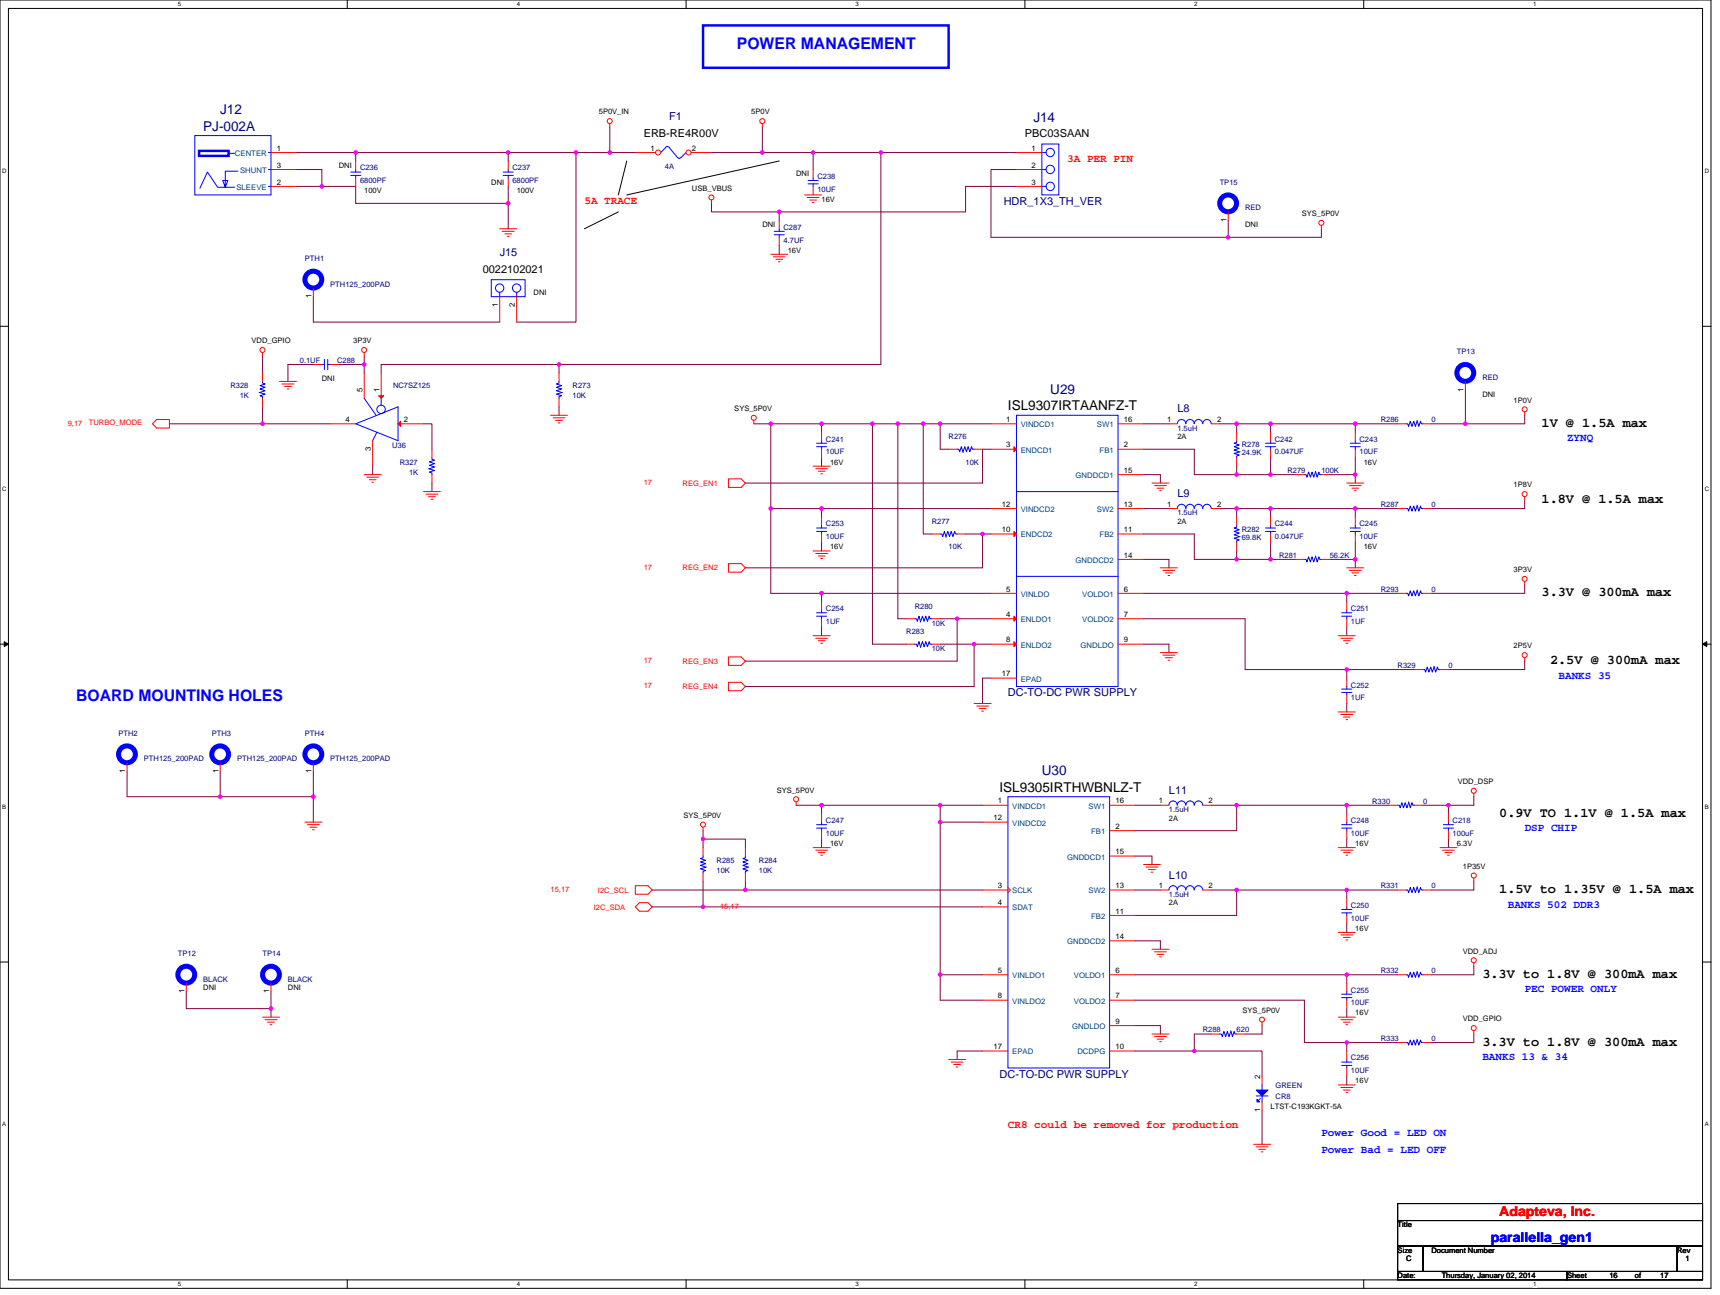
[picture p29: page 16]

EPAD 17
DC-TO-DC PWR SUPPLY

CR8 could be removed for production

Power Good = LED ON
Power Bad = LED OFF

# RESET GENERATION

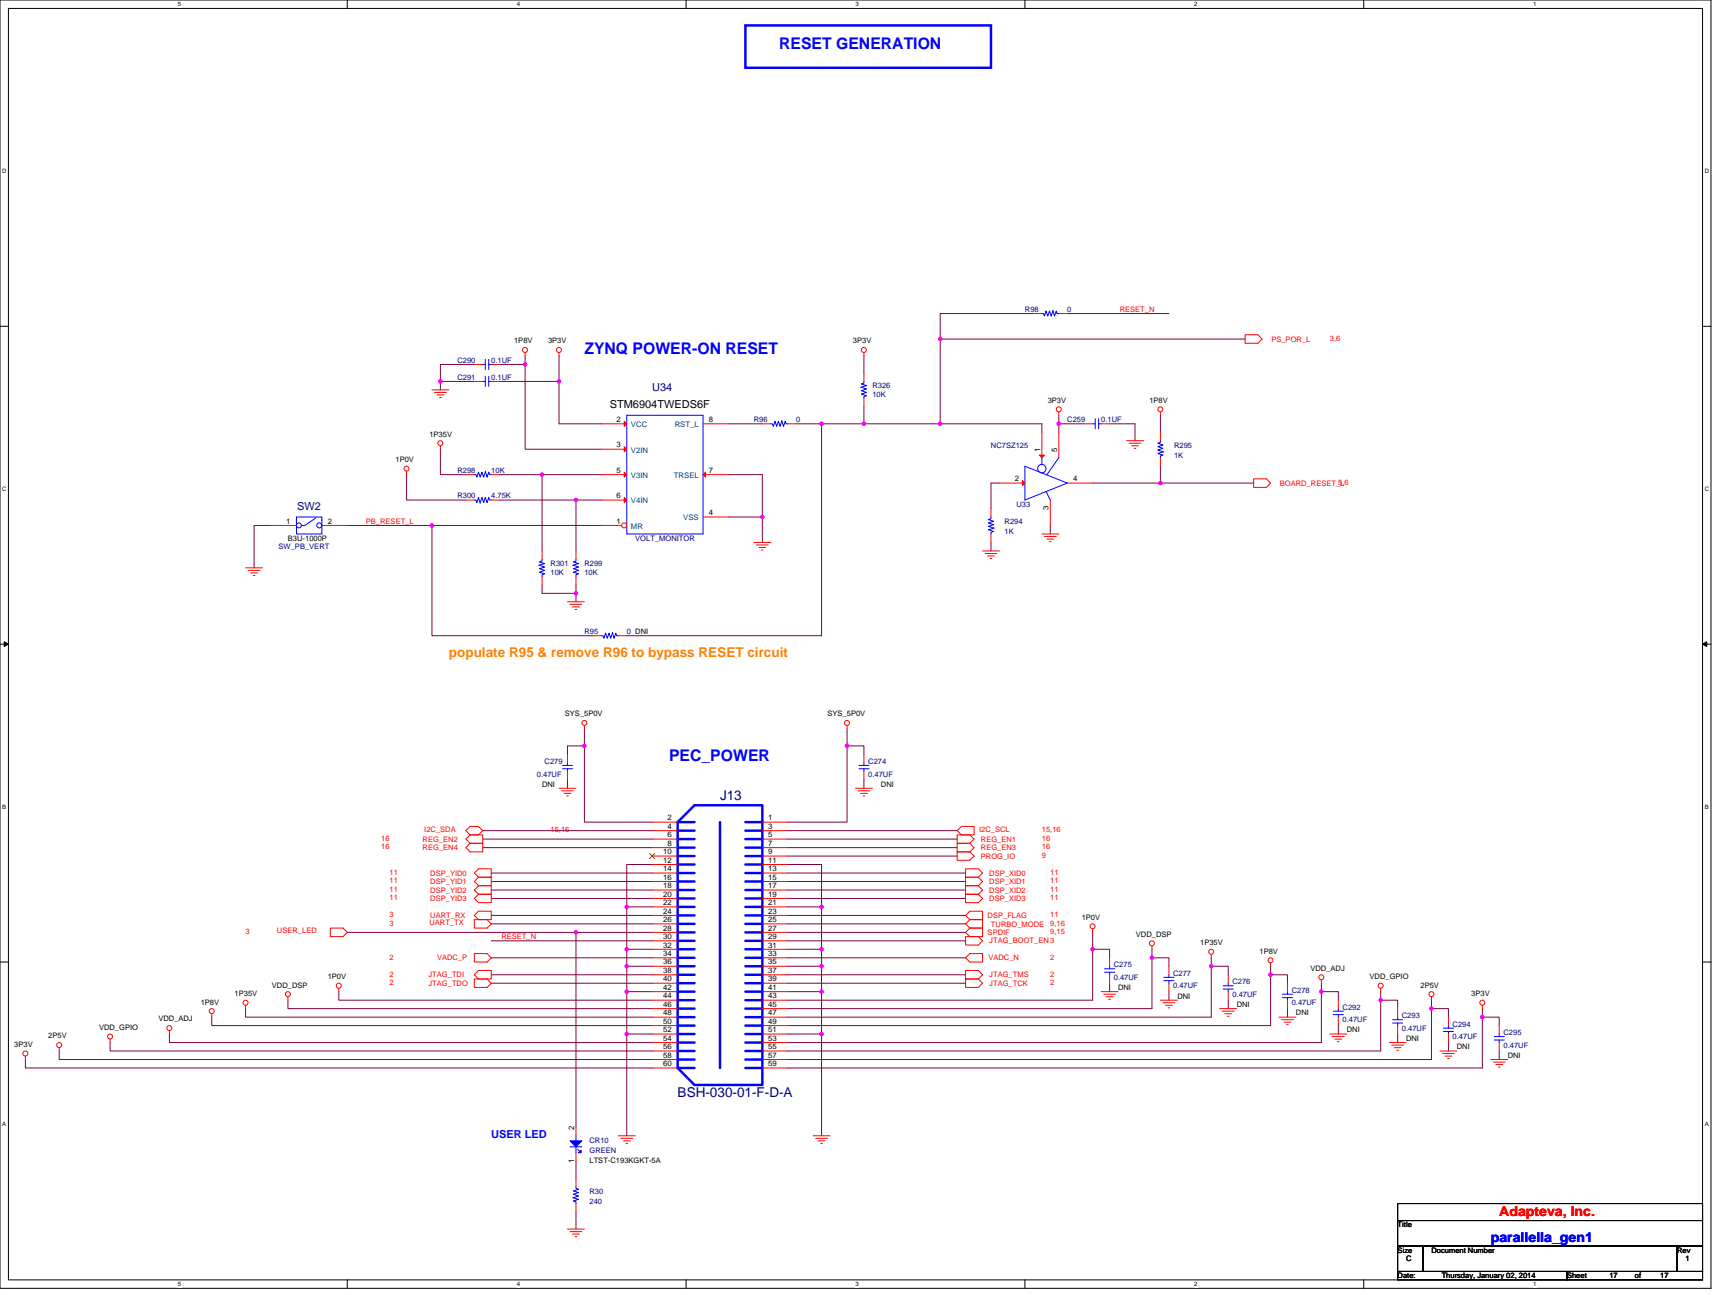
[picture p30: page 17]

ZYNQ POWER-ON RESET

populate R95 & remove R96 to bypass RESET circuit
